Holtshad20/OMC_WIFI/AutoConnect/docs/images/rest_client.png

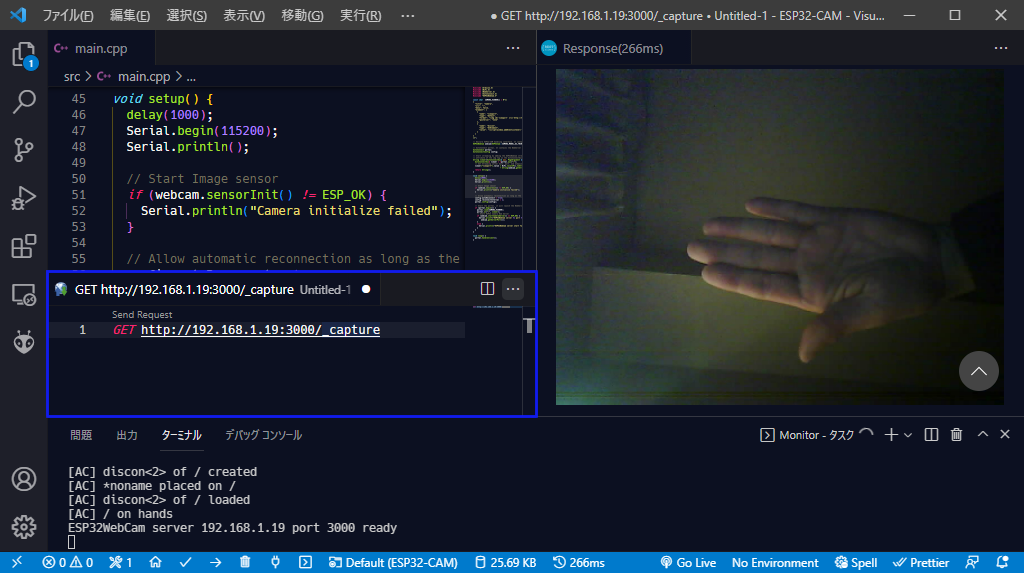
AutoConnect/docs/images/rest_client.png
