Holtshad20/OMC_WIFI/AutoConnect/docs/images/vscode_clean.png

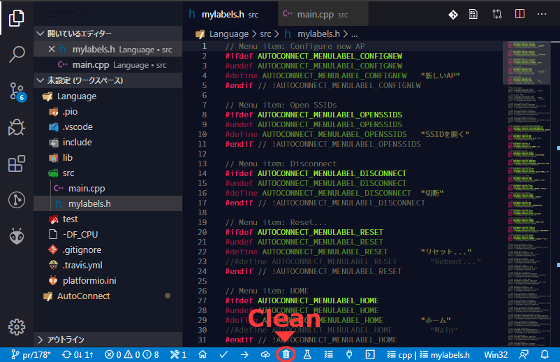
AutoConnect/docs/images/vscode_clean.png
