Holtshad20/OMC_WIFI/1.1 PZEM.jpeg

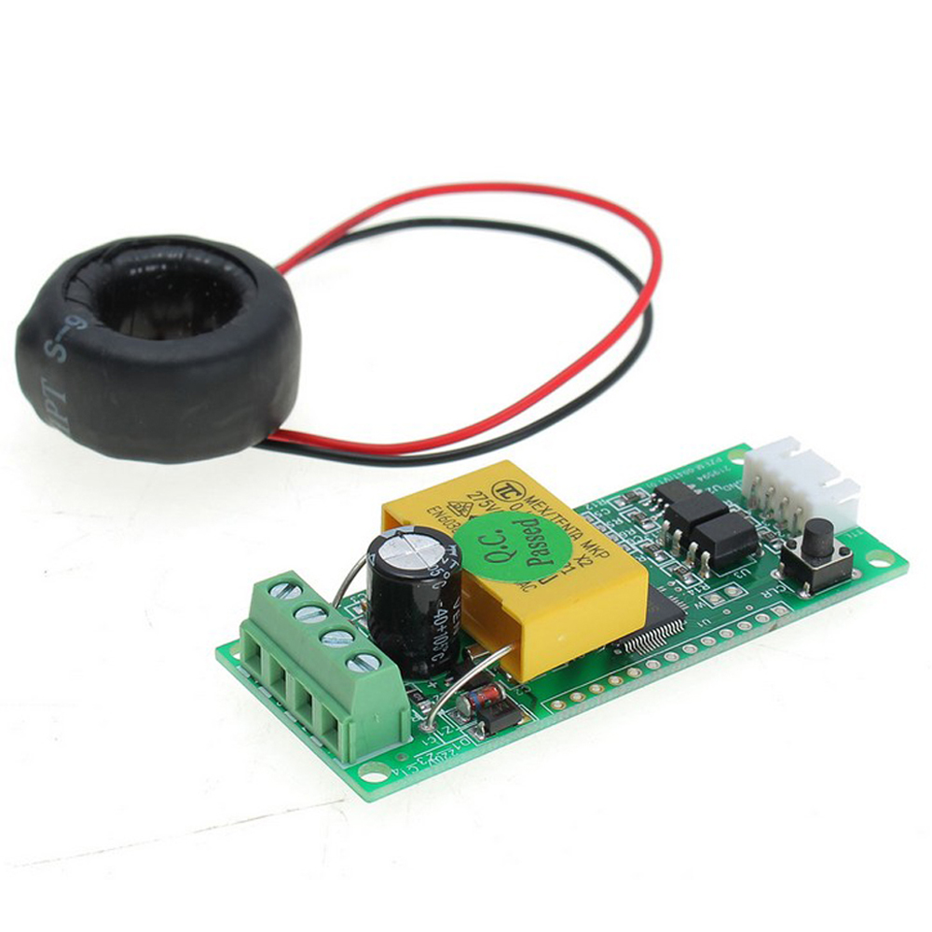
1.1 PZEM.jpeg
