Holtshad20/OMC_WIFI/1.2 SLA.jpg

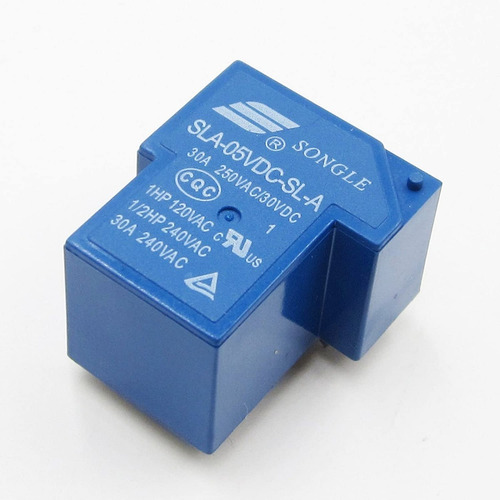
1.2 SLA.jpg
