Holtshad20/OMC_WIFI/1.3 HLK-PM01.jpg

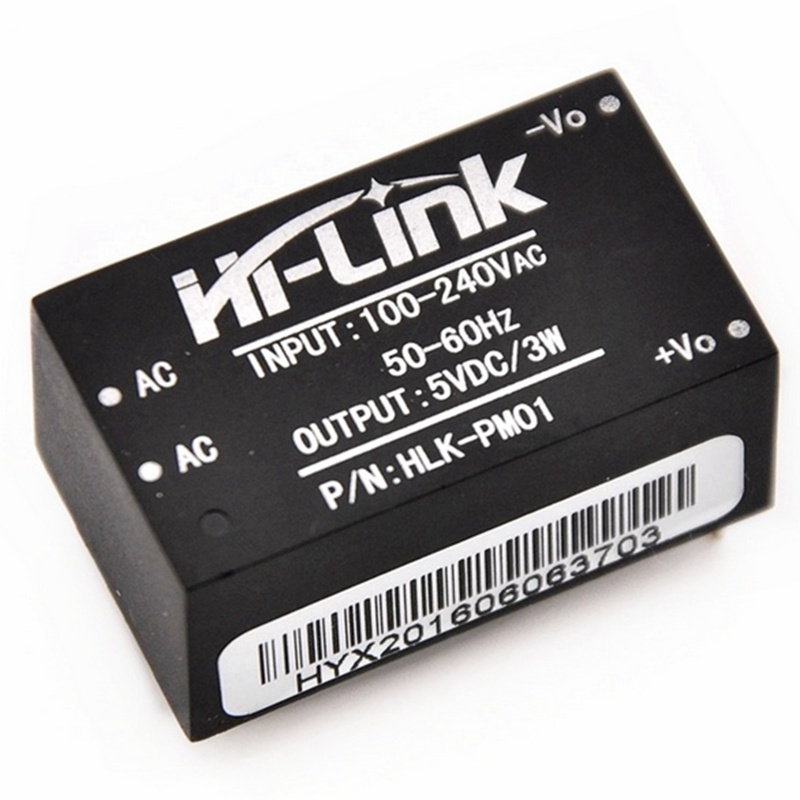
1.3 HLK-PM01.jpg
