Holtshad20/OMC_WIFI/AutoConnect/docs/images/ac2.gif

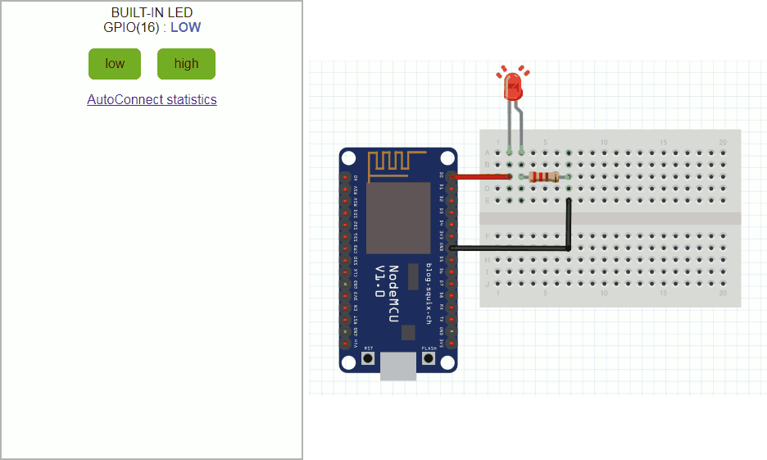
AutoConnect/docs/images/ac2.gif
