Holtshad20/OMC_WIFI/AutoConnect/docs/images/ac.png

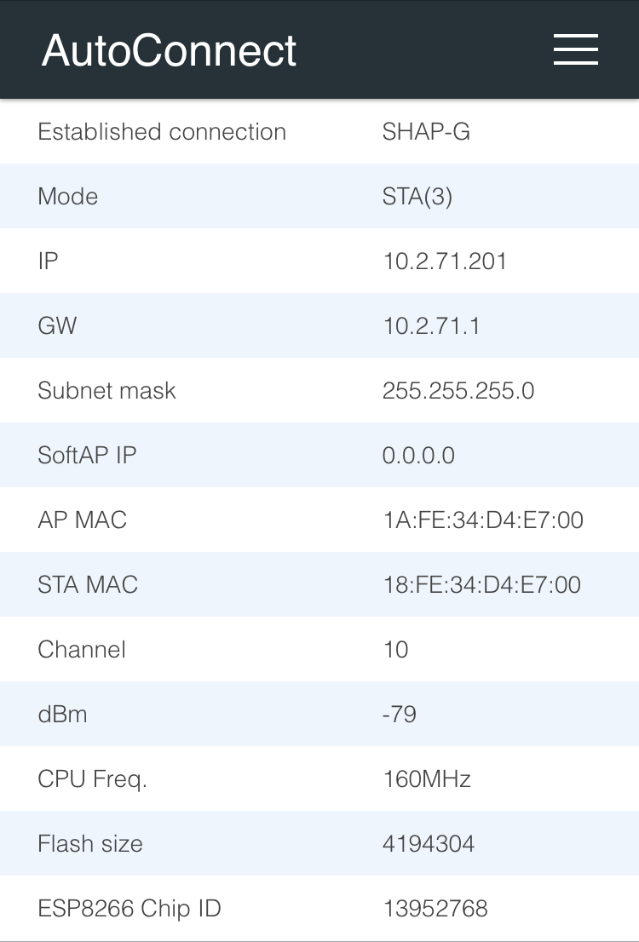
AutoConnect/docs/images/ac.png
