Holtshad20/OMC_WIFI/AutoConnect/docs/images/ac_auxmenu.png

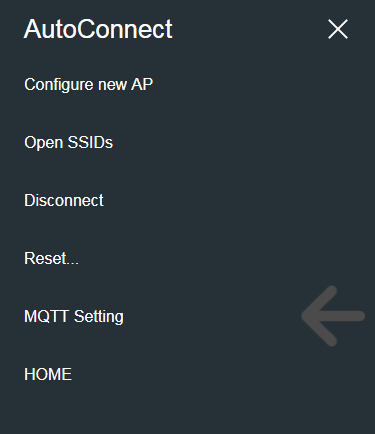
AutoConnect/docs/images/ac_auxmenu.png
