Holtshad20/OMC_WIFI/AutoConnect/docs/images/ac_auxmenu_multi.png

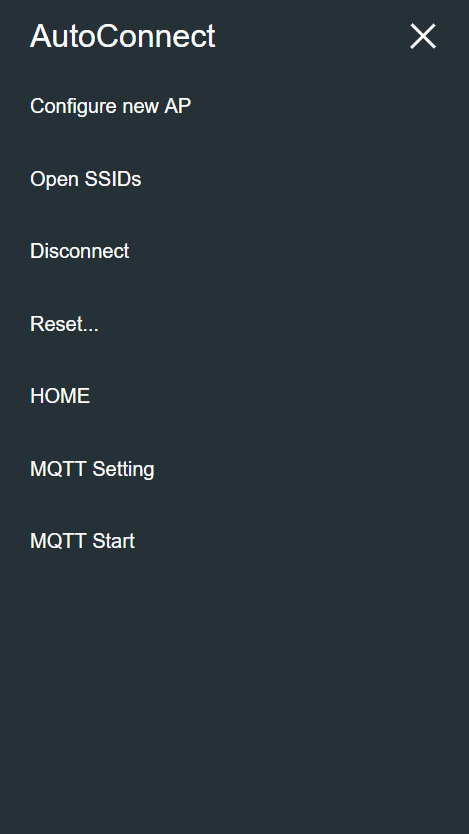
AutoConnect/docs/images/ac_auxmenu_multi.png
