Holtshad20/OMC_WIFI/AutoConnect/docs/images/ac_json.png

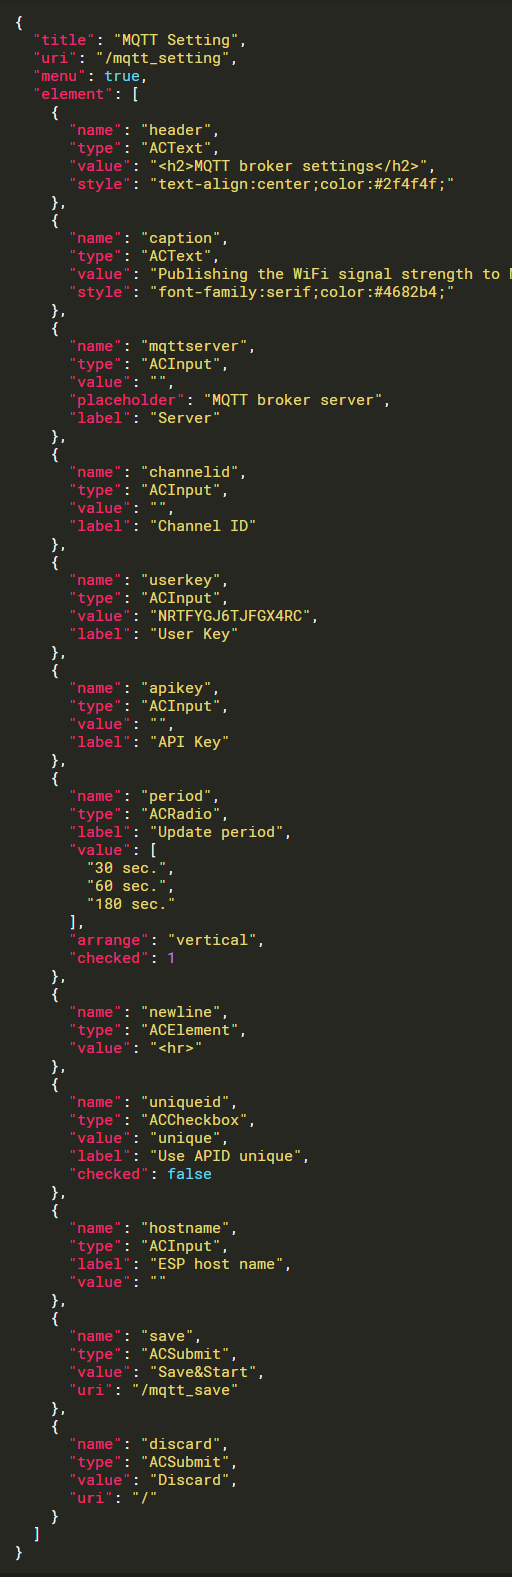
AutoConnect/docs/images/ac_json.png
