Holtshad20/OMC_WIFI/AutoConnect/docs/images/ac_mqtt_setting.png

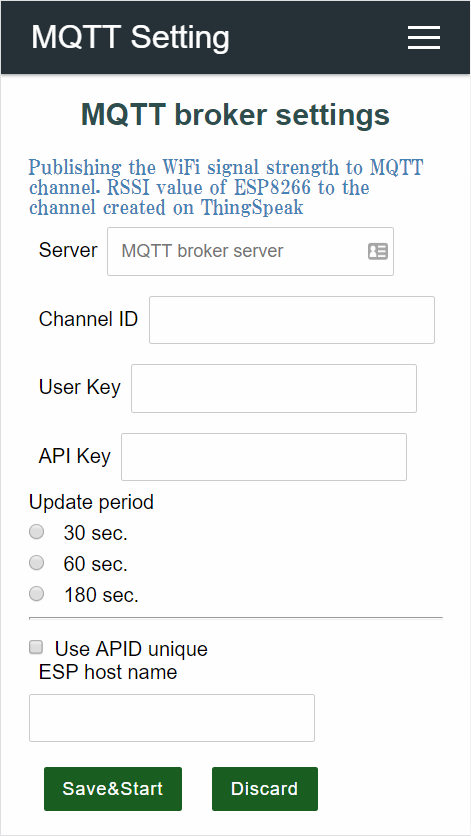
AutoConnect/docs/images/ac_mqtt_setting.png
