Holtshad20/OMC_WIFI/AutoConnect/docs/images/ACMenu_indigo.png

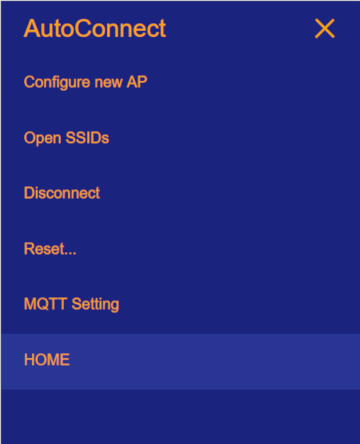
AutoConnect/docs/images/ACMenu_indigo.png
