Holtshad20/OMC_WIFI/AutoConnect/docs/images/acow.png

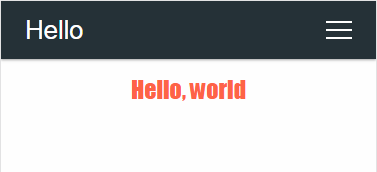
AutoConnect/docs/images/acow.png
