Holtshad20/OMC_WIFI/AutoConnect/docs/images/acselect.png

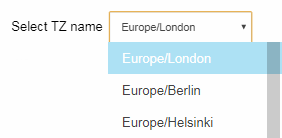
AutoConnect/docs/images/acselect.png
