Holtshad20/OMC_WIFI/AutoConnect/docs/images/adder.png

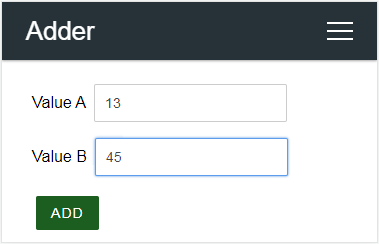
AutoConnect/docs/images/adder.png
