Holtshad20/OMC_WIFI/AutoConnect/docs/images/addmenu.gif

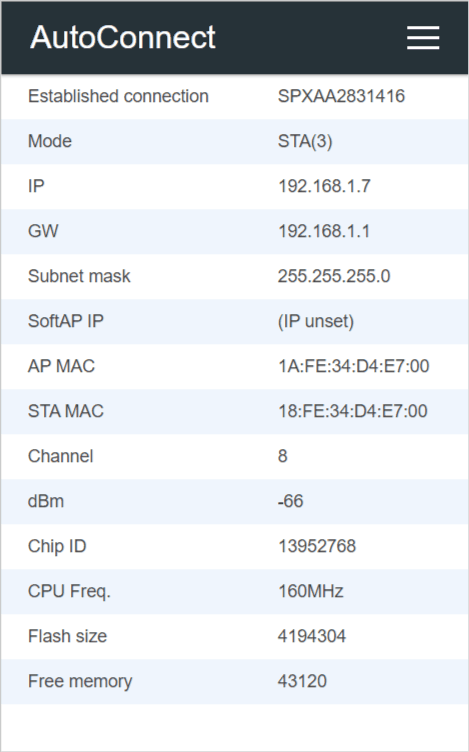
AutoConnect/docs/images/addmenu.gif
