Holtshad20/OMC_WIFI/AutoConnect/docs/images/answer.png

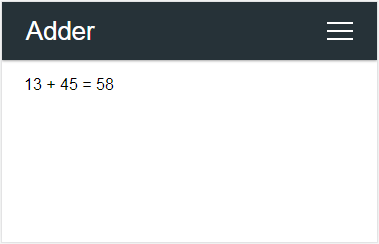
AutoConnect/docs/images/answer.png
