Holtshad20/OMC_WIFI/AutoConnect/docs/images/APIKeys.png

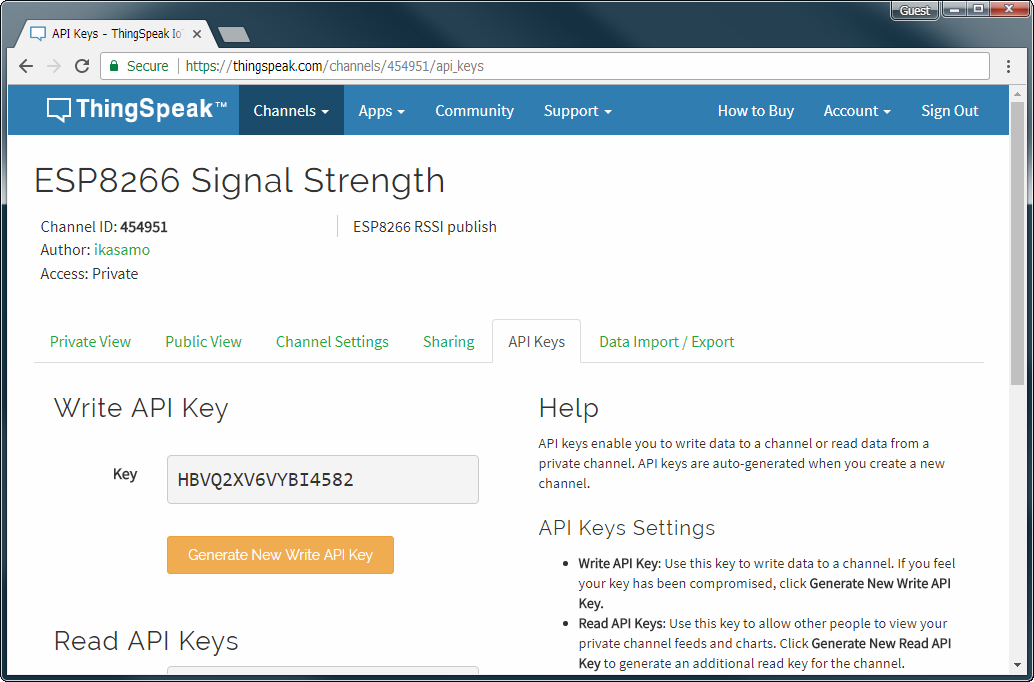
AutoConnect/docs/images/APIKeys.png
