Holtshad20/OMC_WIFI/AutoConnect/docs/images/applymenu.png

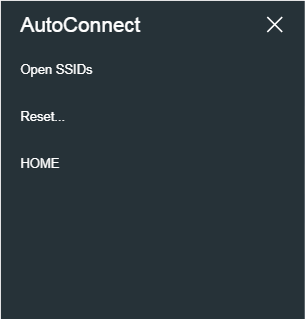
AutoConnect/docs/images/applymenu.png
