Holtshad20/OMC_WIFI/AutoConnect/docs/images/AutoConnectAux.gif

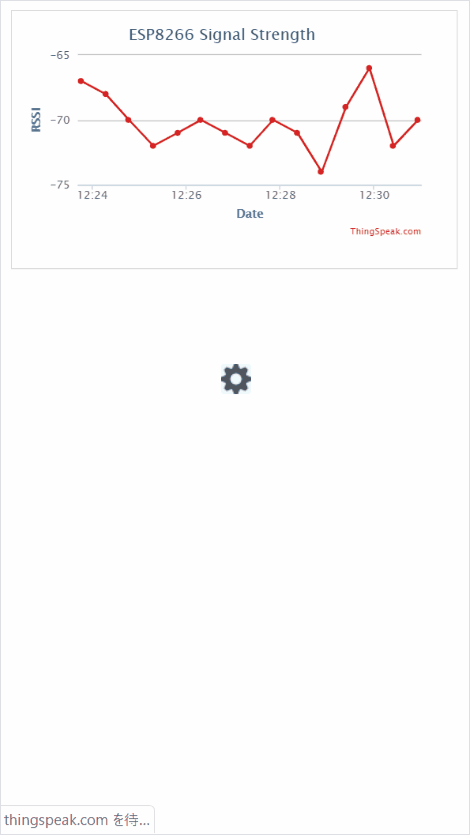
AutoConnect/docs/images/AutoConnectAux.gif
