Holtshad20/OMC_WIFI/AutoConnect/docs/images/aux_fsbrowser.gif

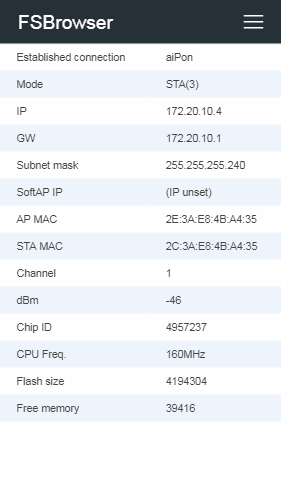
AutoConnect/docs/images/aux_fsbrowser.gif
