Holtshad20/OMC_WIFI/AutoConnect/docs/images/aux_json.png

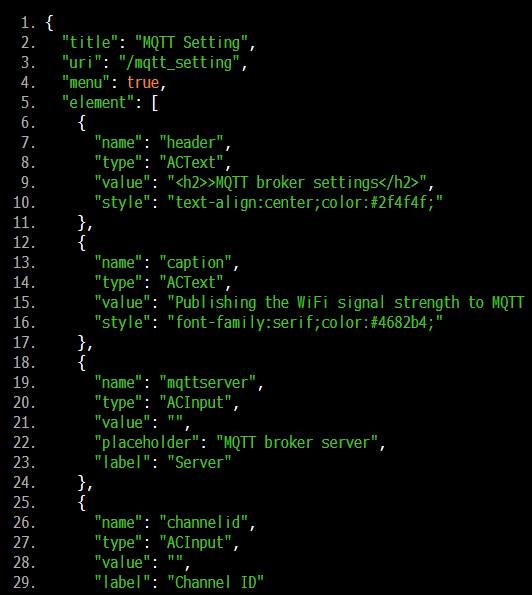
AutoConnect/docs/images/aux_json.png
