Holtshad20/OMC_WIFI/AutoConnect/docs/images/aux_ov.gif

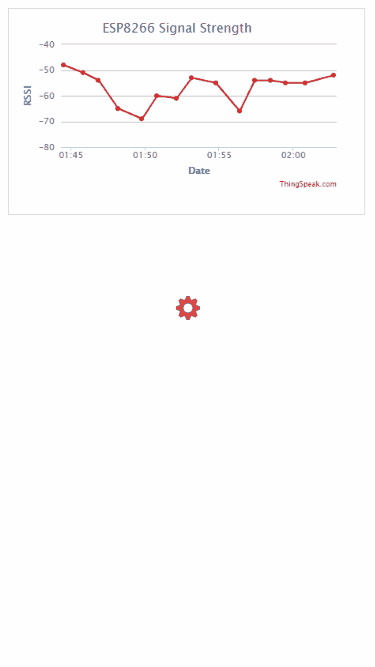
AutoConnect/docs/images/aux_ov.gif
