Holtshad20/OMC_WIFI/AutoConnect/docs/images/aux_pattern.gif

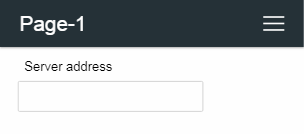
AutoConnect/docs/images/aux_pattern.gif
