Holtshad20/OMC_WIFI/AutoConnect/docs/images/beforeafter.png

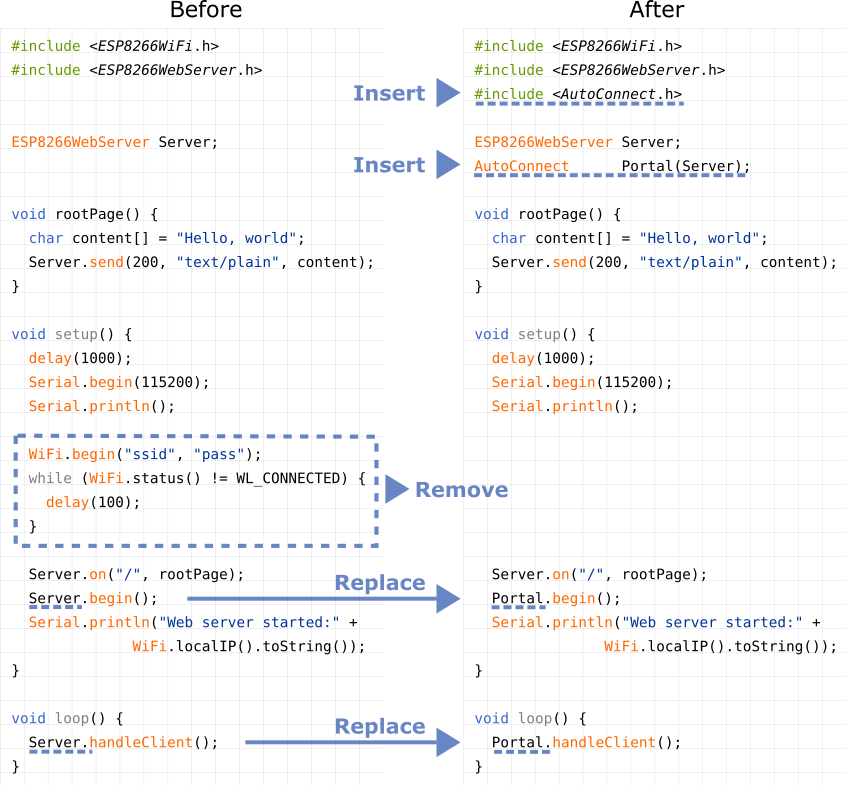
AutoConnect/docs/images/beforeafter.png
