Holtshad20/OMC_WIFI/AutoConnect/docs/images/begin.png

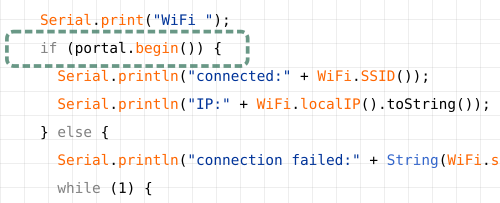
AutoConnect/docs/images/begin.png
