Holtshad20/OMC_WIFI/AutoConnect/docs/images/ChannelID.png

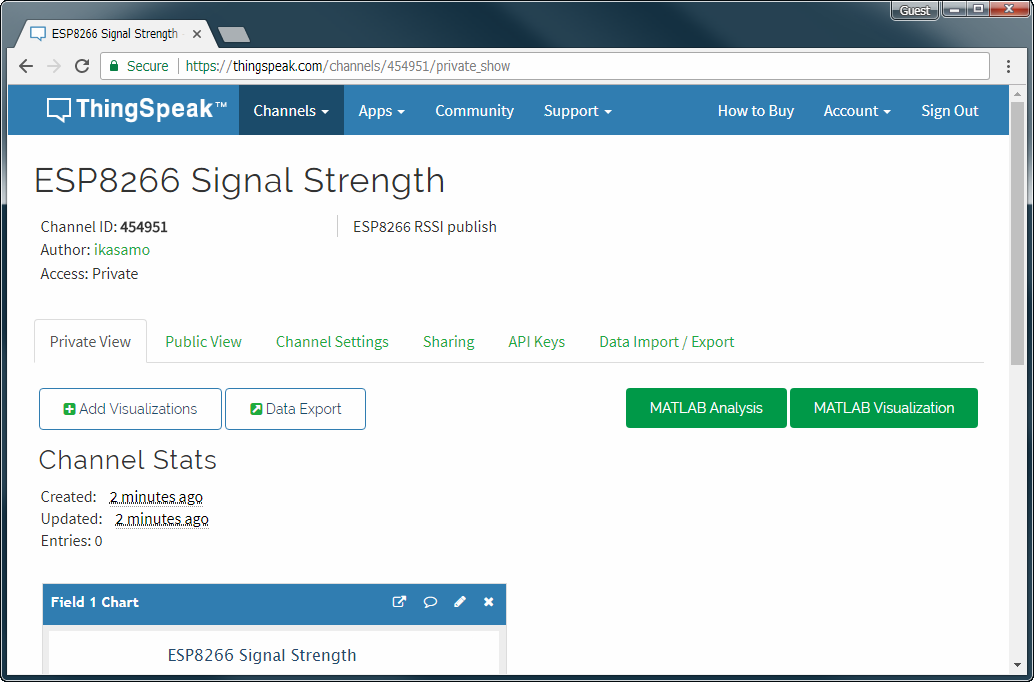
AutoConnect/docs/images/ChannelID.png
