Holtshad20/OMC_WIFI/AutoConnect/docs/images/ChannelStatus.png

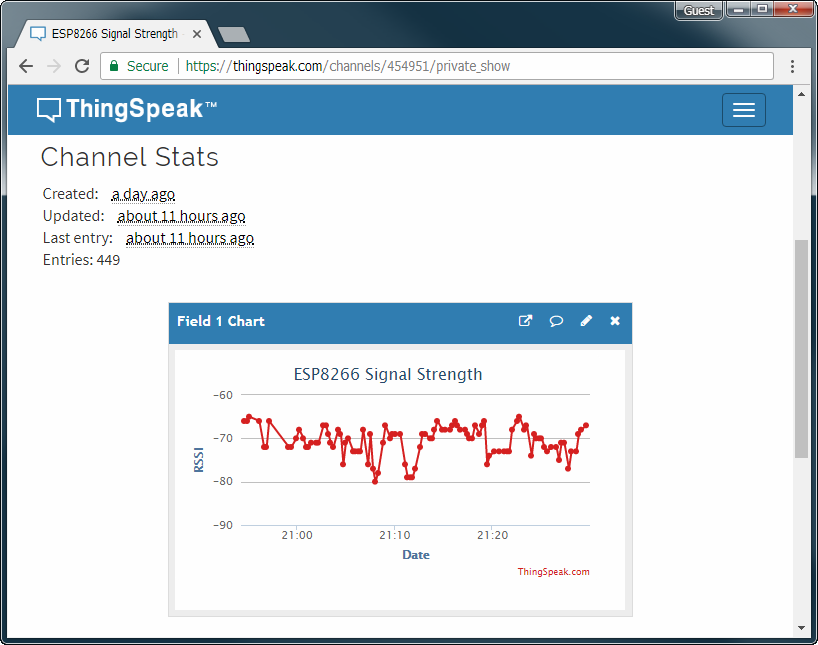
AutoConnect/docs/images/ChannelStatus.png
