Holtshad20/OMC_WIFI/AutoConnect/docs/images/config_ssid.png

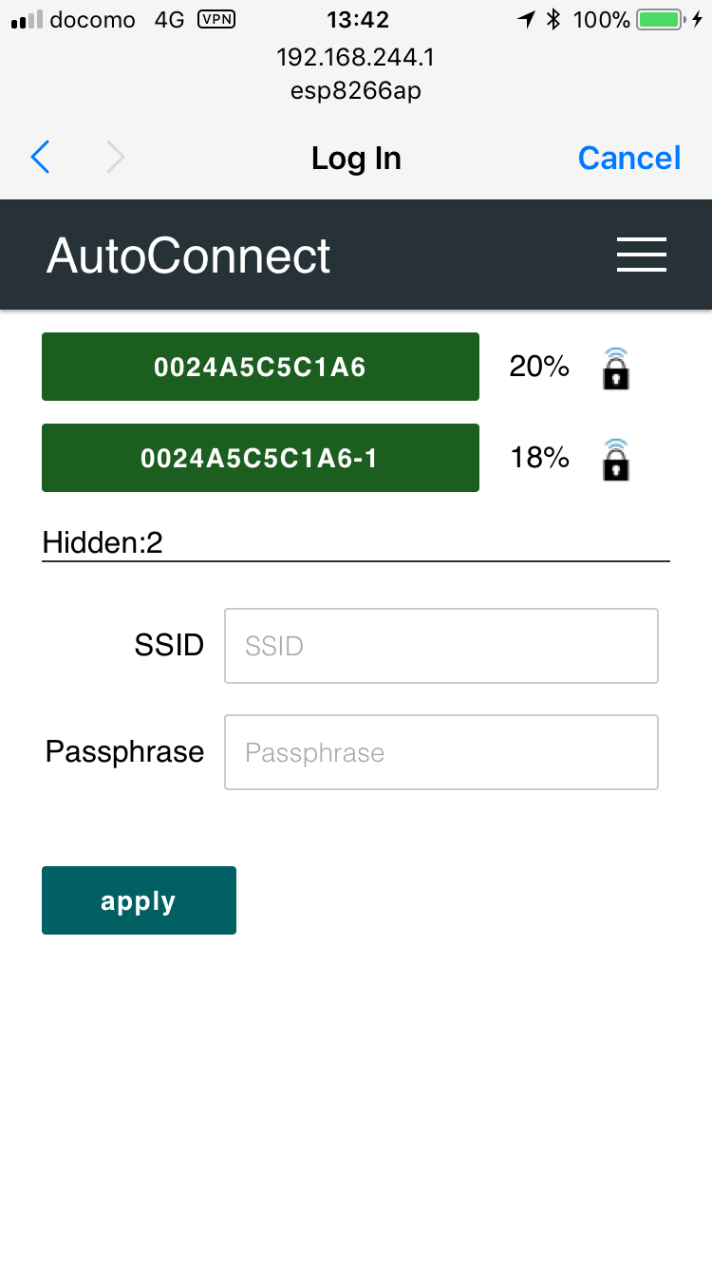
AutoConnect/docs/images/config_ssid.png
