Holtshad20/OMC_WIFI/AutoConnect/docs/images/confignew.png

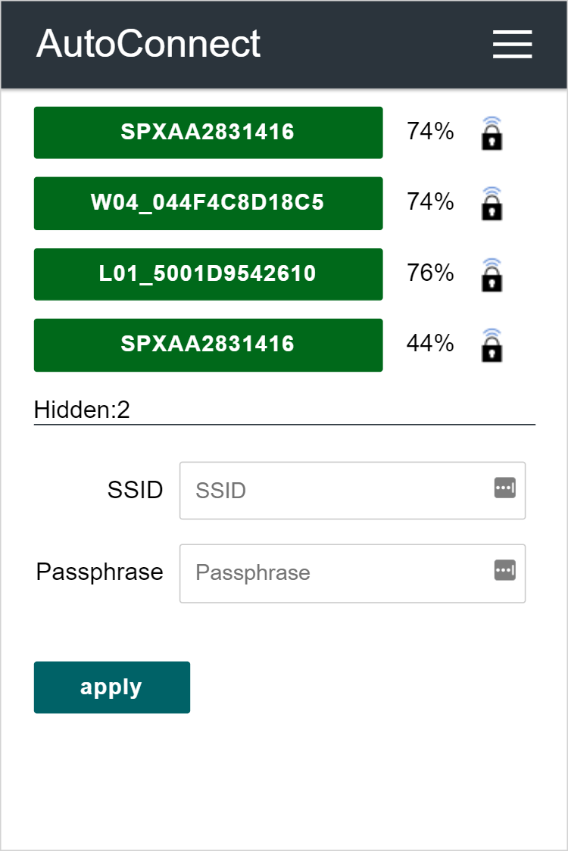
AutoConnect/docs/images/confignew.png
