Holtshad20/OMC_WIFI/AutoConnect/docs/images/CreateChannel.png

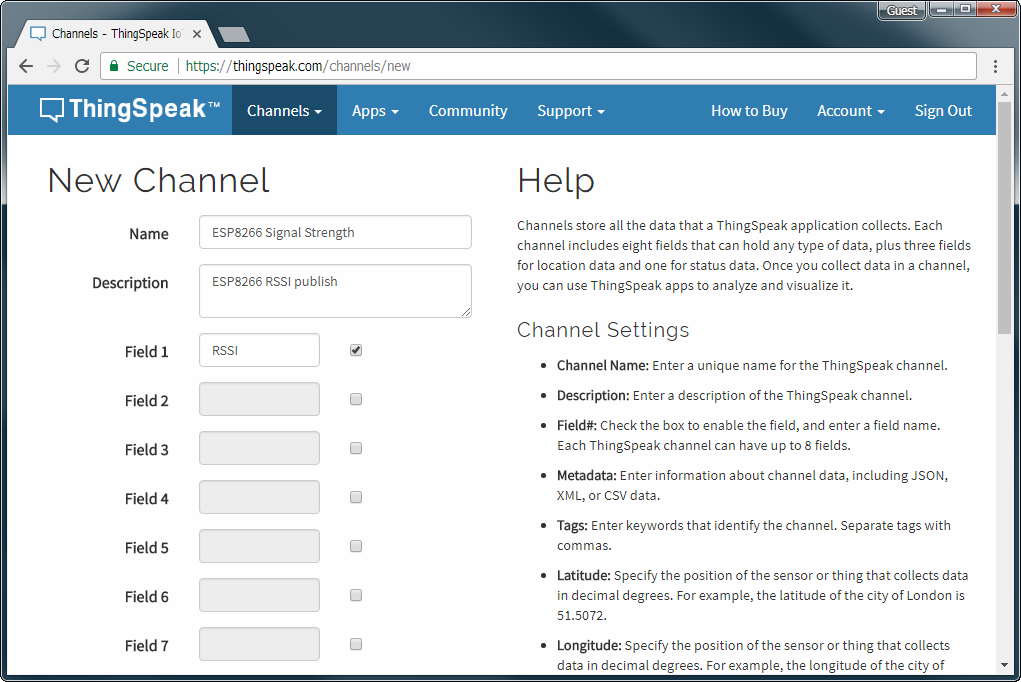
AutoConnect/docs/images/CreateChannel.png
