Holtshad20/OMC_WIFI/AutoConnect/docs/images/creditmigrate.png

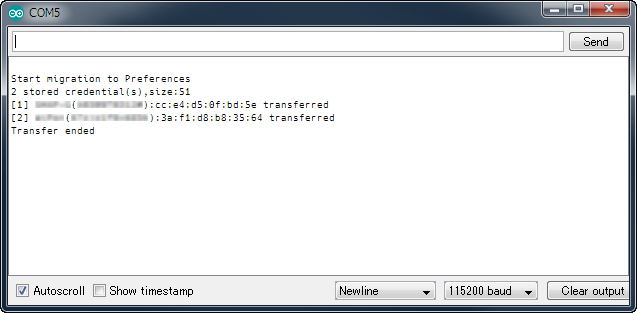
AutoConnect/docs/images/creditmigrate.png
