Holtshad20/OMC_WIFI/AutoConnect/docs/images/esp32cam_view.png

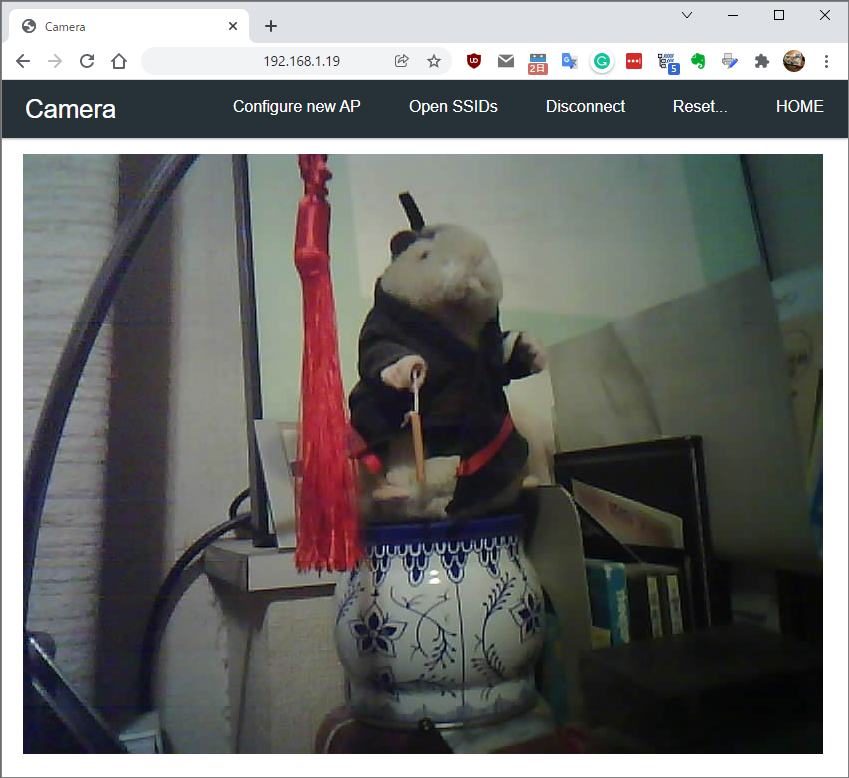
AutoConnect/docs/images/esp32cam_view.png
