Holtshad20/OMC_WIFI/AutoConnect/docs/images/espshaker.gif

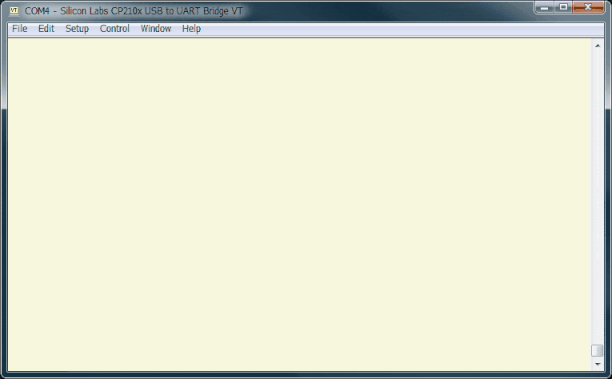
AutoConnect/docs/images/espshaker.gif
