Holtshad20/OMC_WIFI/AutoConnect/docs/images/established.png

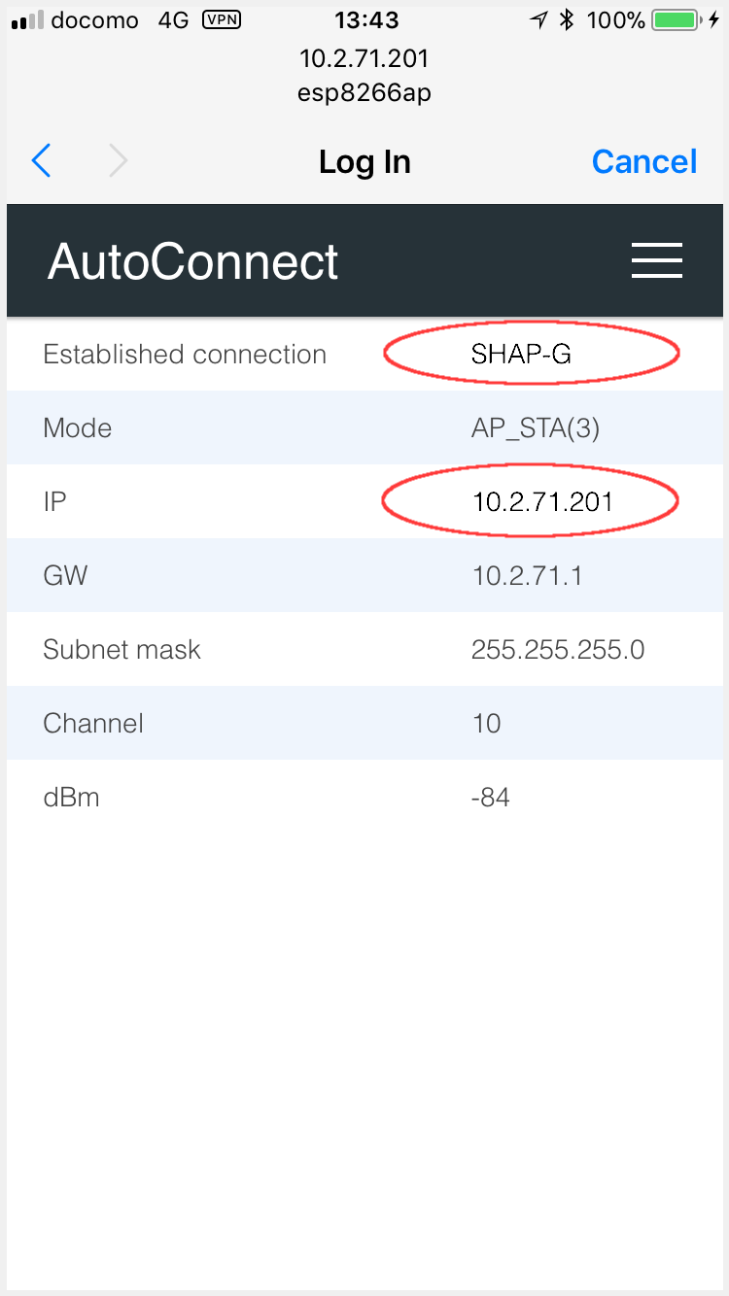
AutoConnect/docs/images/established.png
