Holtshad20/OMC_WIFI/AutoConnect/docs/images/export_binary.png

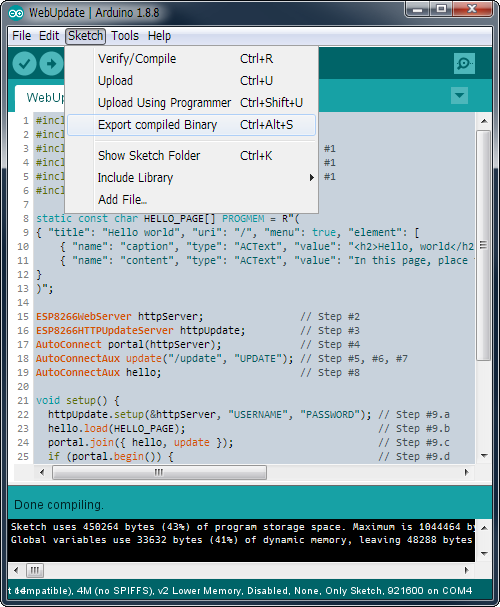
AutoConnect/docs/images/export_binary.png
