Holtshad20/OMC_WIFI/AutoConnect/docs/images/extswitch.png

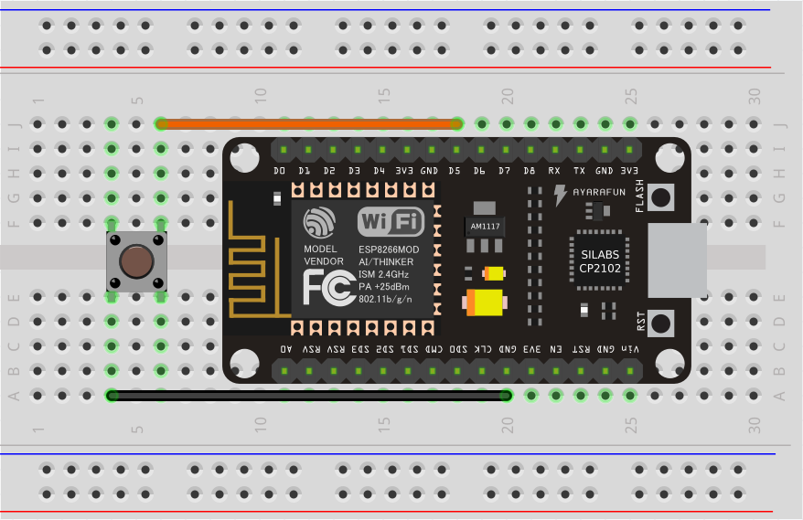
AutoConnect/docs/images/extswitch.png
