Holtshad20/OMC_WIFI/AutoConnect/docs/images/gitrepo.png

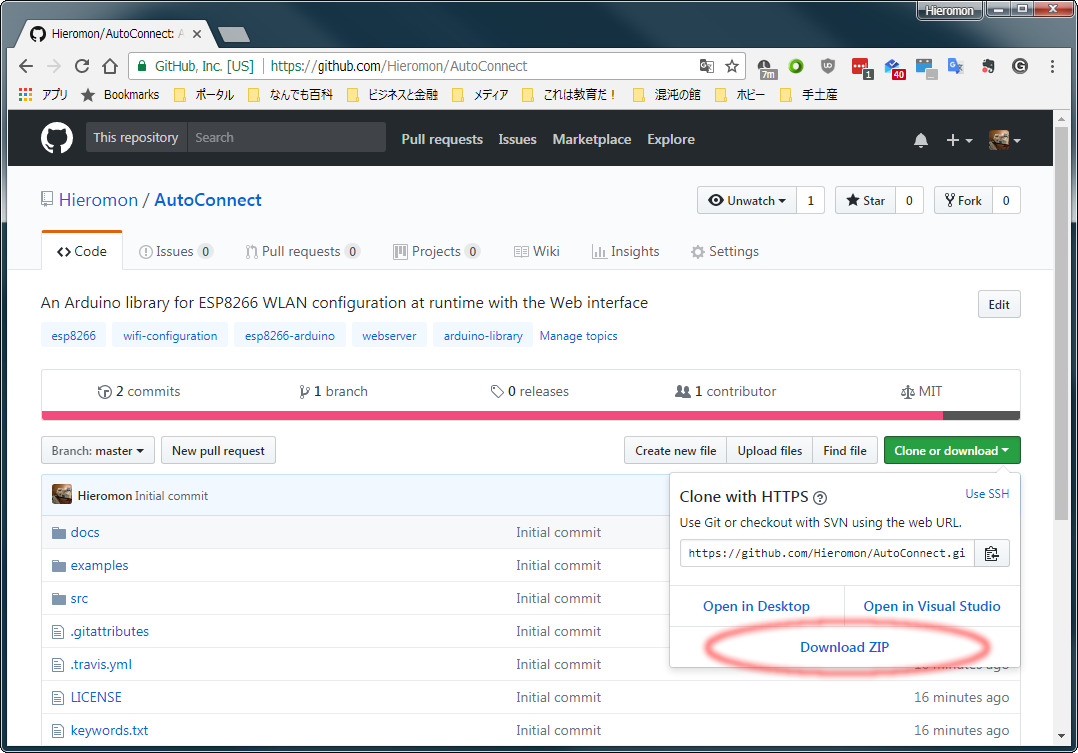
AutoConnect/docs/images/gitrepo.png
