Holtshad20/OMC_WIFI/AutoConnect/docs/images/global1.png

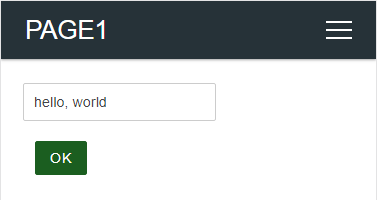
AutoConnect/docs/images/global1.png
