Holtshad20/OMC_WIFI/AutoConnect/docs/images/global2.png

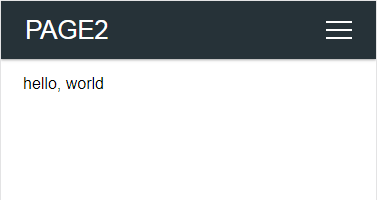
AutoConnect/docs/images/global2.png
