Holtshad20/OMC_WIFI/AutoConnect/docs/images/handleClient.png

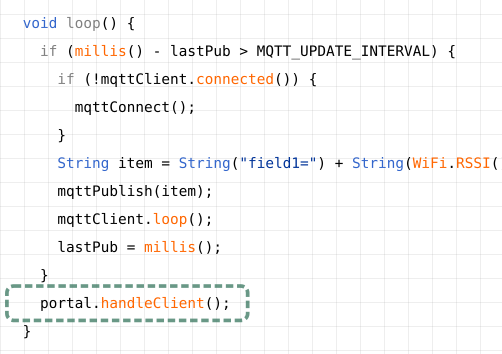
AutoConnect/docs/images/handleClient.png
