Holtshad20/OMC_WIFI/AutoConnect/docs/images/heartbeat.png

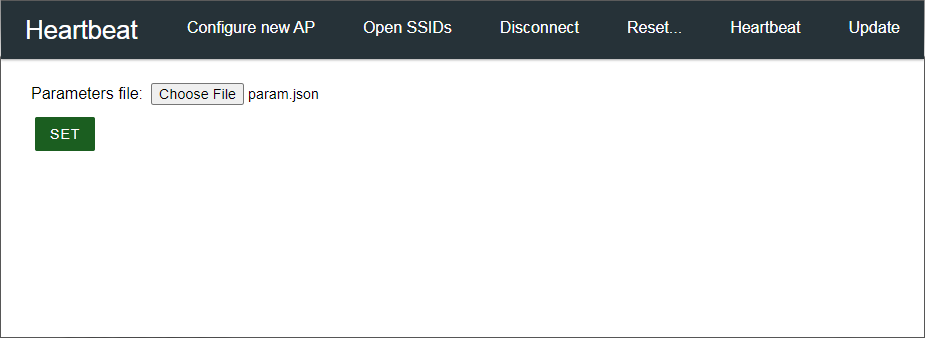
AutoConnect/docs/images/heartbeat.png
