Holtshad20/OMC_WIFI/AutoConnect/docs/images/hello_world.png

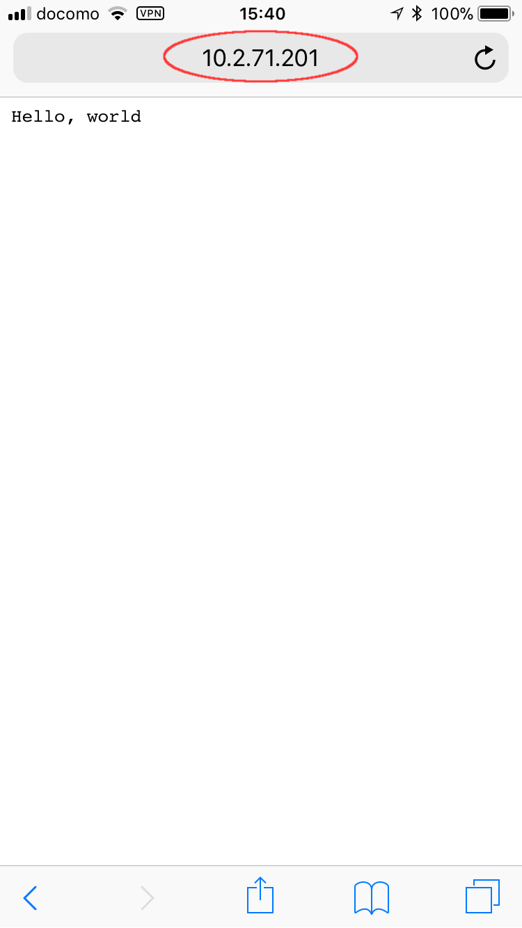
AutoConnect/docs/images/hello_world.png
