Holtshad20/OMC_WIFI/AutoConnect/docs/images/html5_forms_number.png

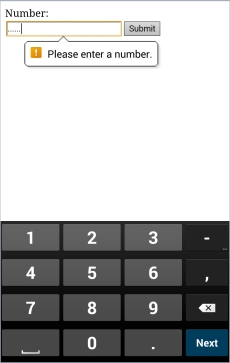
AutoConnect/docs/images/html5_forms_number.png
