Holtshad20/OMC_WIFI/AutoConnect/docs/images/html5_forms_number_ios.png

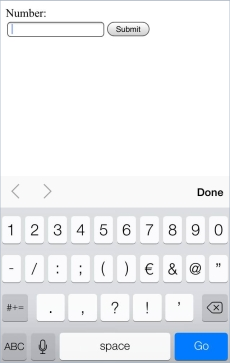
AutoConnect/docs/images/html5_forms_number_ios.png
