Holtshad20/OMC_WIFI/AutoConnect/docs/images/include.png

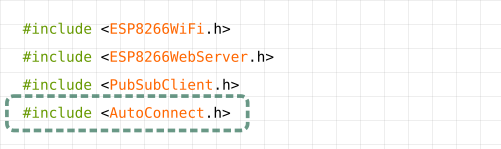
AutoConnect/docs/images/include.png
