Holtshad20/OMC_WIFI/AutoConnect/docs/images/ins_lib.png

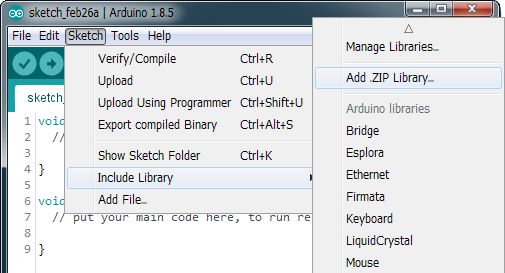
AutoConnect/docs/images/ins_lib.png
