Holtshad20/OMC_WIFI/AutoConnect/docs/images/lm.png

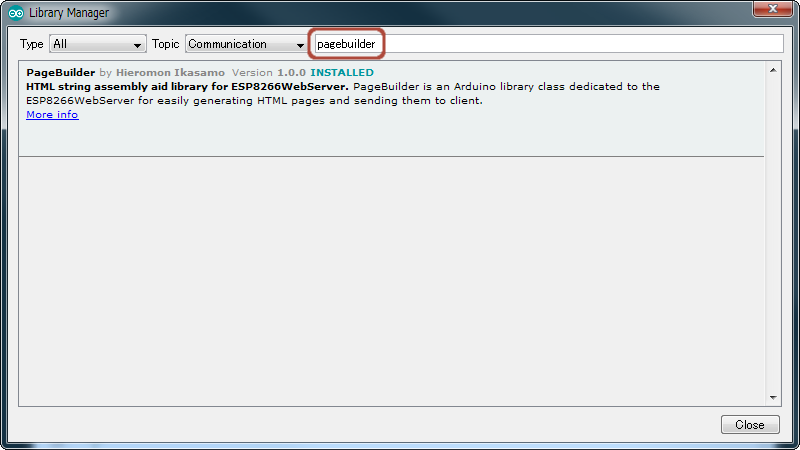
AutoConnect/docs/images/lm.png
