Holtshad20/OMC_WIFI/AutoConnect/docs/images/localize.png

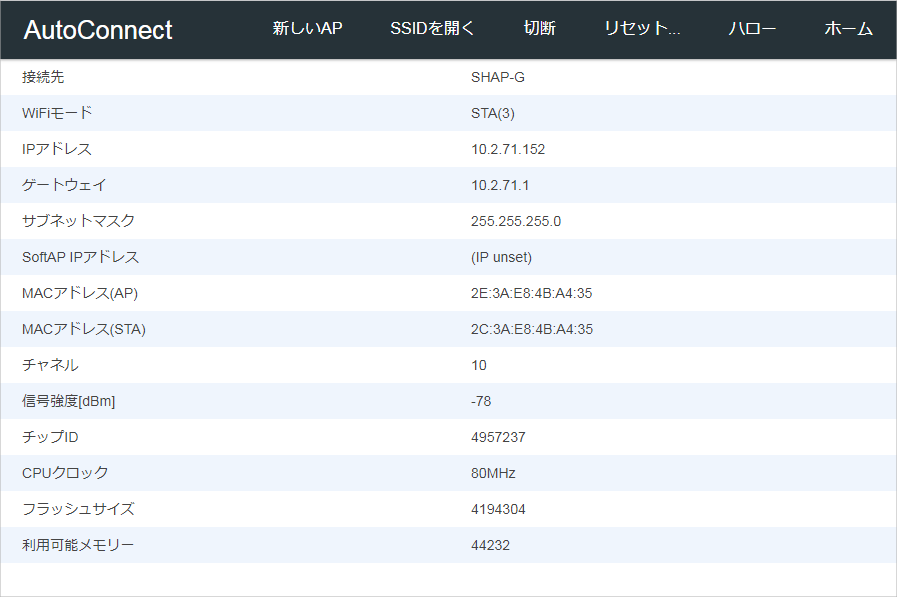
AutoConnect/docs/images/localize.png
