Holtshad20/OMC_WIFI/AutoConnect/docs/images/login.png

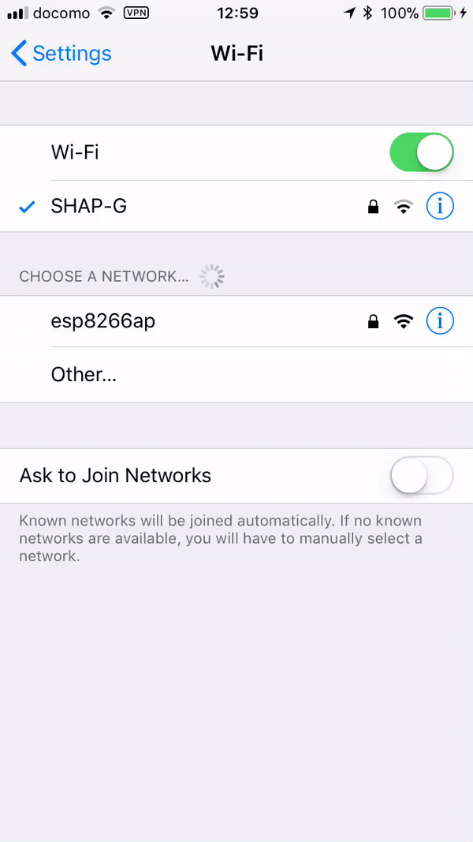
AutoConnect/docs/images/login.png
