Holtshad20/OMC_WIFI/AutoConnect/docs/images/menu_home.png

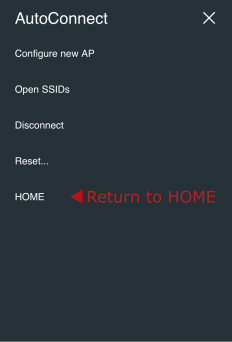
AutoConnect/docs/images/menu_home.png
