Holtshad20/OMC_WIFI/AutoConnect/docs/images/menu_login.png

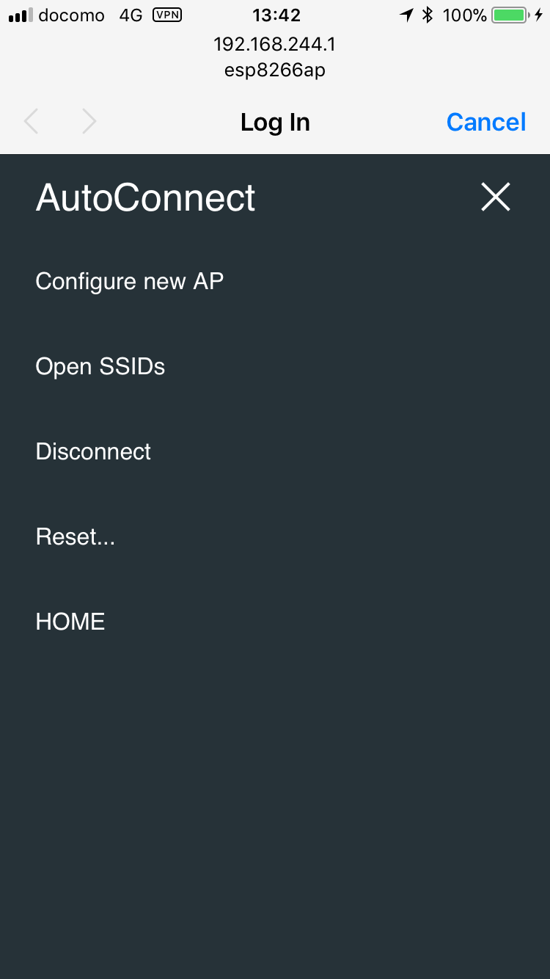
AutoConnect/docs/images/menu_login.png
