Holtshad20/OMC_WIFI/AutoConnect/docs/images/newap.png

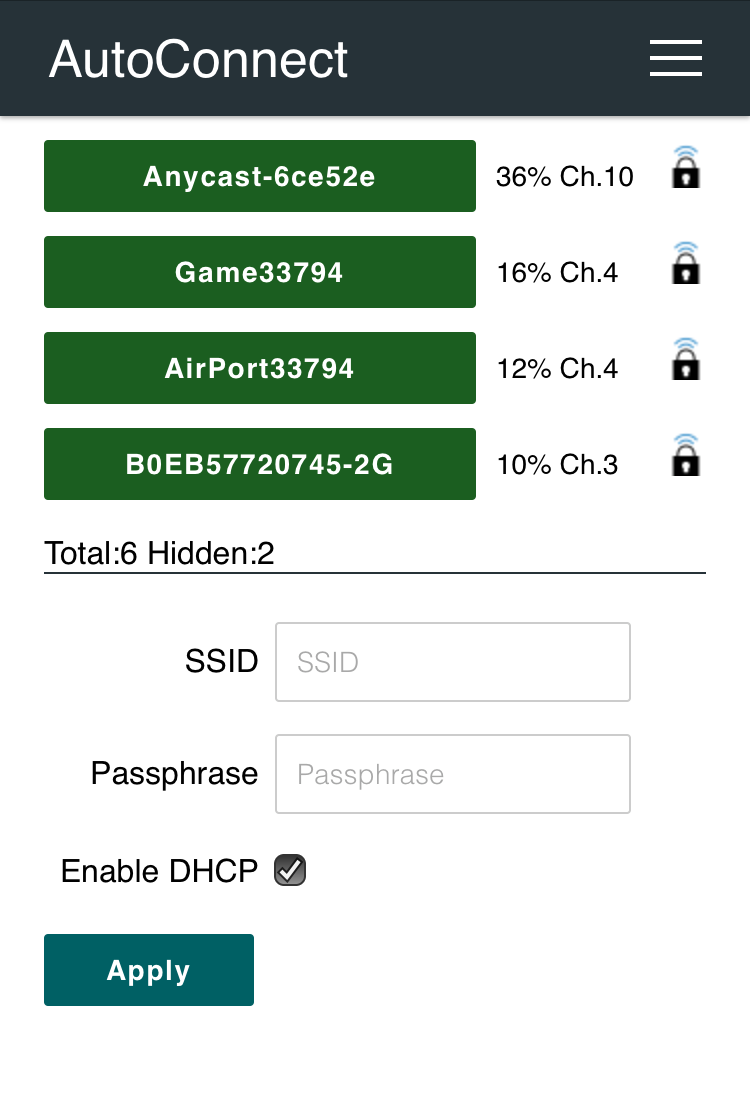
AutoConnect/docs/images/newap.png
