Holtshad20/OMC_WIFI/AutoConnect/docs/images/newap_static.png

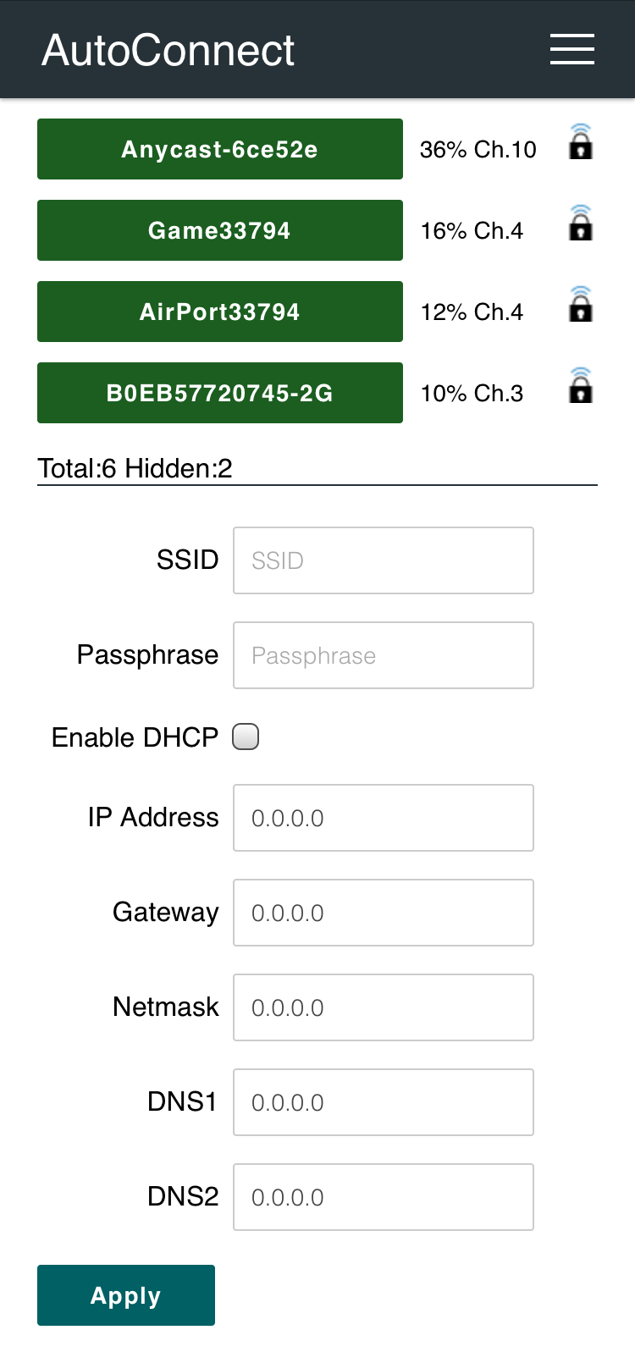
AutoConnect/docs/images/newap_static.png
