Holtshad20/OMC_WIFI/AutoConnect/docs/images/openssid.png

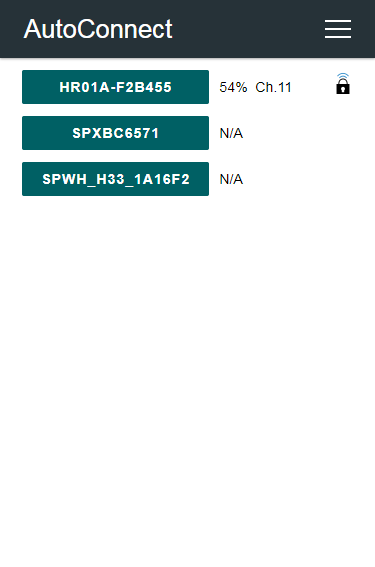
AutoConnect/docs/images/openssid.png
