Holtshad20/OMC_WIFI/AutoConnect/docs/images/openssid_trash.png

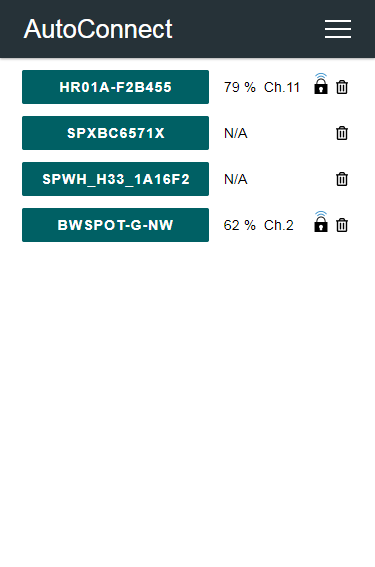
AutoConnect/docs/images/openssid_trash.png
