Holtshad20/OMC_WIFI/AutoConnect/docs/images/otacaption.png

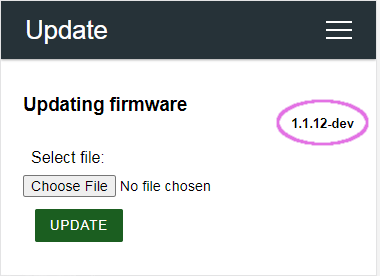
AutoConnect/docs/images/otacaption.png
