Holtshad20/OMC_WIFI/AutoConnect/docs/images/ov.gif

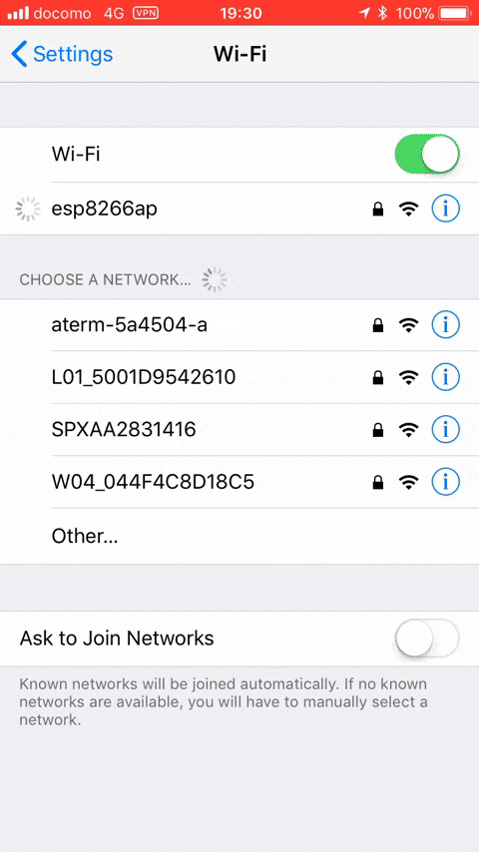
AutoConnect/docs/images/ov.gif
