Holtshad20/OMC_WIFI/AutoConnect/docs/images/ov.png

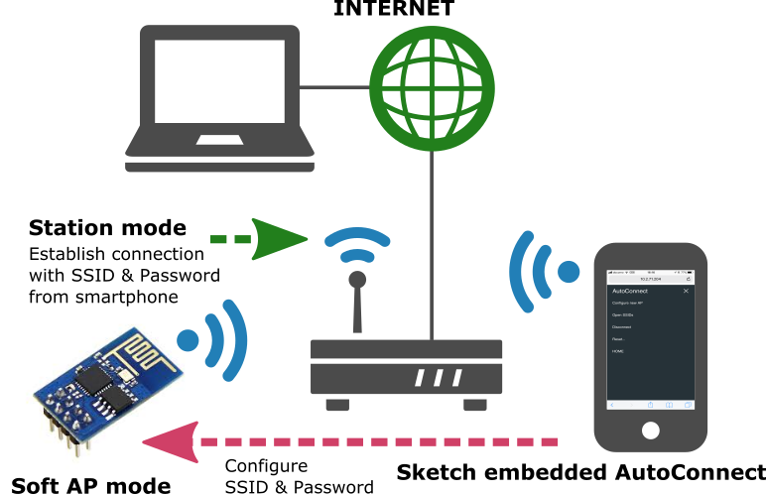
AutoConnect/docs/images/ov.png
