Holtshad20/OMC_WIFI/AutoConnect/docs/images/partition.png

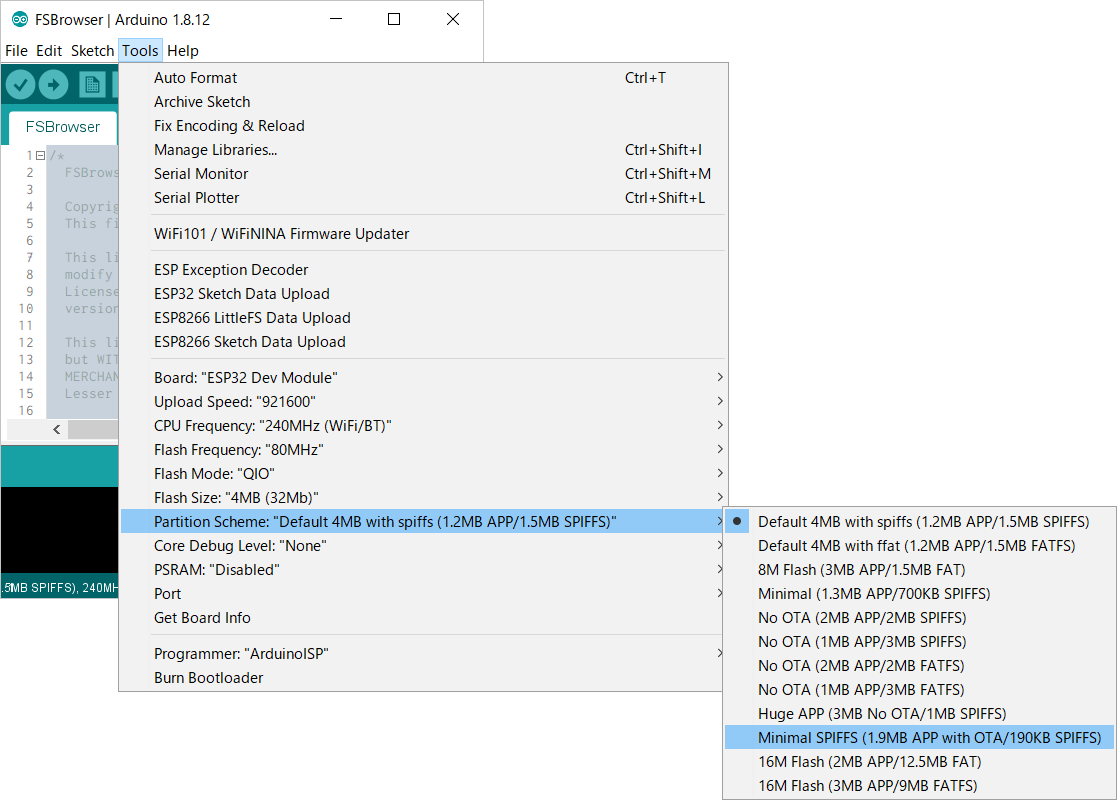
AutoConnect/docs/images/partition.png
