Holtshad20/OMC_WIFI/AutoConnect/docs/images/reset.png

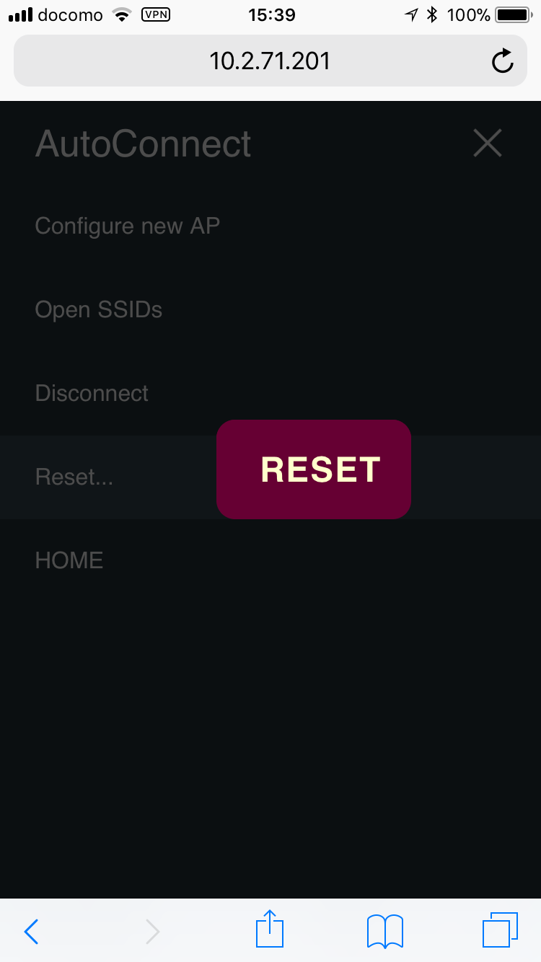
AutoConnect/docs/images/reset.png
