Holtshad20/OMC_WIFI/AutoConnect/docs/images/reset_r.png

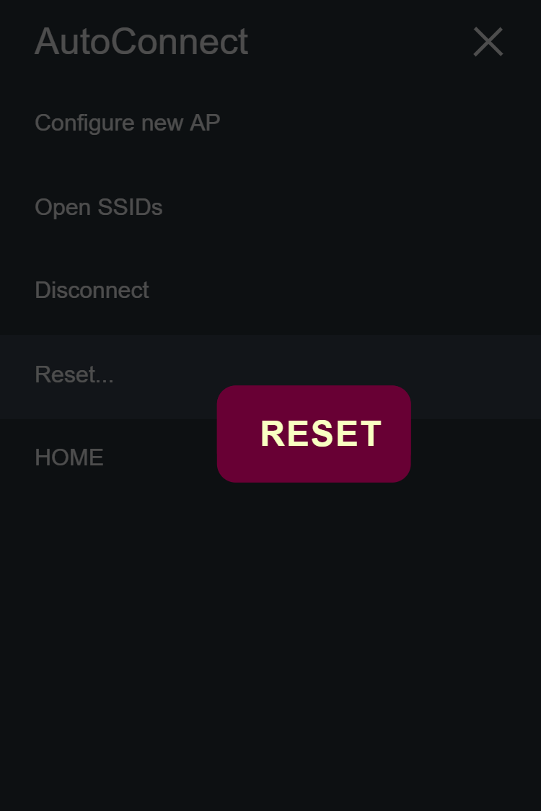
AutoConnect/docs/images/reset_r.png
