Holtshad20/OMC_WIFI/AutoConnect/docs/images/resetting.png

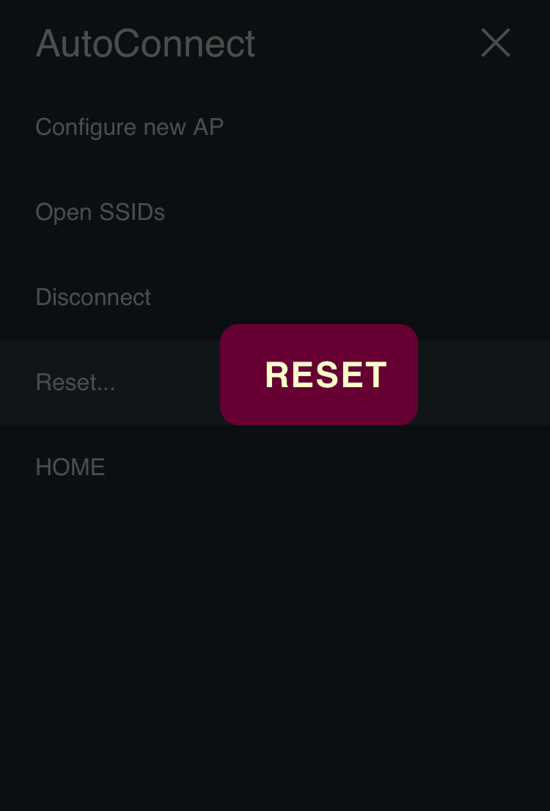
AutoConnect/docs/images/resetting.png
