Holtshad20/OMC_WIFI/AutoConnect/docs/images/rssi_chart.png

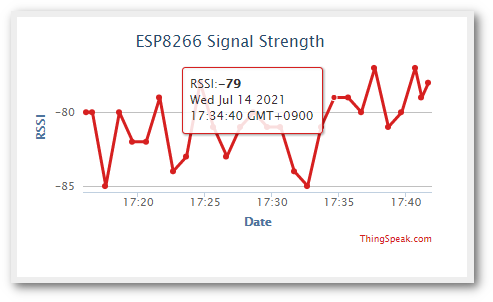
AutoConnect/docs/images/rssi_chart.png
