Holtshad20/OMC_WIFI/AutoConnect/docs/images/serial.png

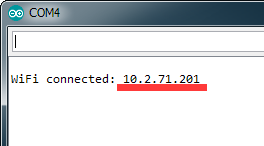
AutoConnect/docs/images/serial.png
