Holtshad20/OMC_WIFI/AutoConnect/docs/images/serverupdate.gif

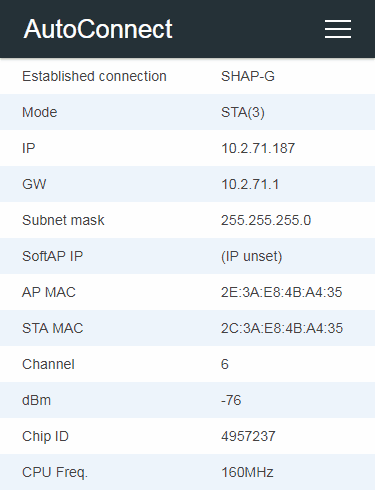
AutoConnect/docs/images/serverupdate.gif
