Holtshad20/OMC_WIFI/AutoConnect/docs/images/stat.png

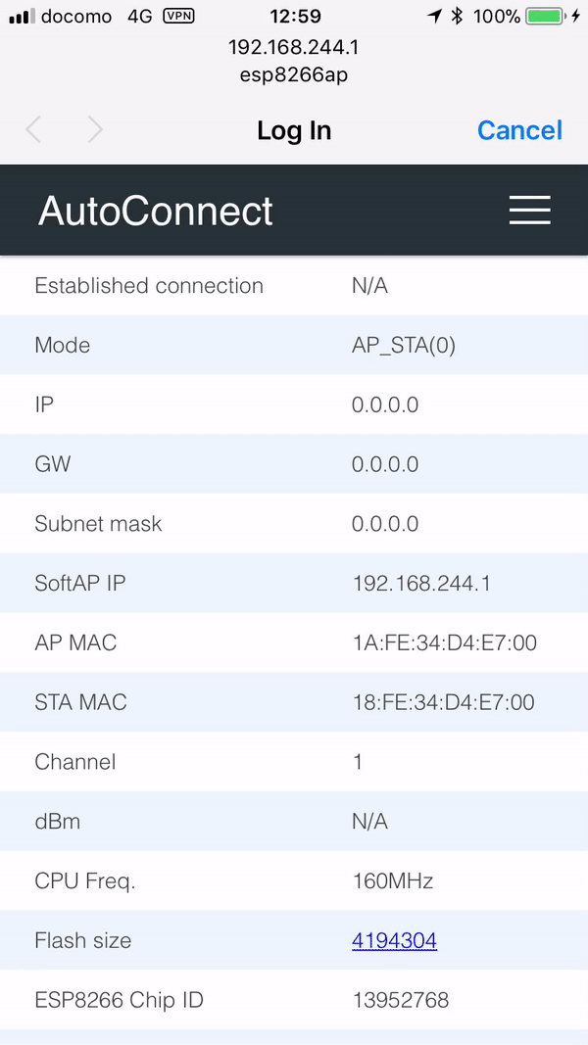
AutoConnect/docs/images/stat.png
