Holtshad20/OMC_WIFI/AutoConnect/docs/images/staticip.png

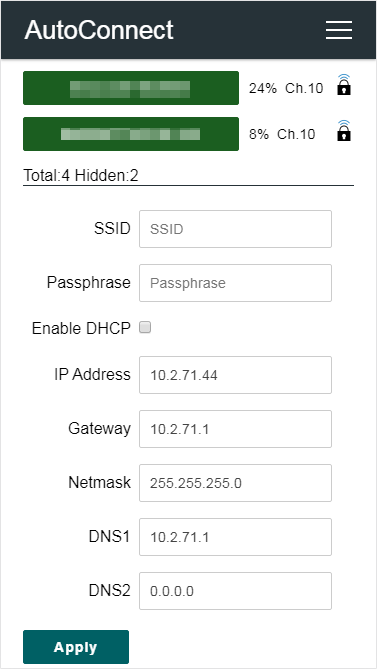
AutoConnect/docs/images/staticip.png
