Holtshad20/OMC_WIFI/AutoConnect/docs/images/statistics.png

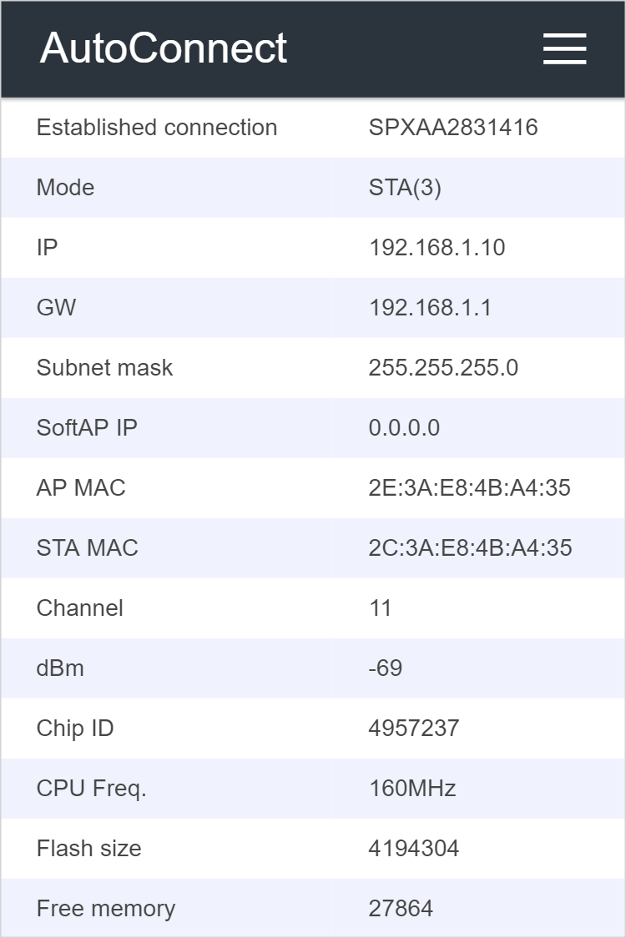
AutoConnect/docs/images/statistics.png
