Holtshad20/OMC_WIFI/AutoConnect/docs/images/updated.png

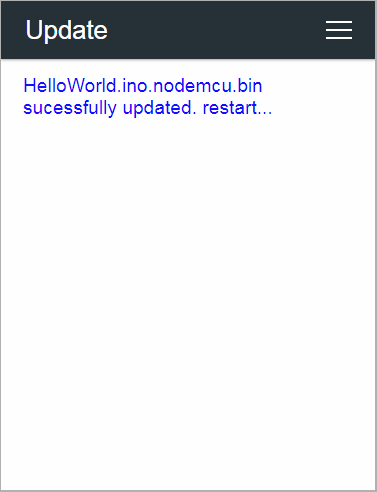
AutoConnect/docs/images/updated.png
