Holtshad20/OMC_WIFI/AutoConnect/docs/images/updatelist.png

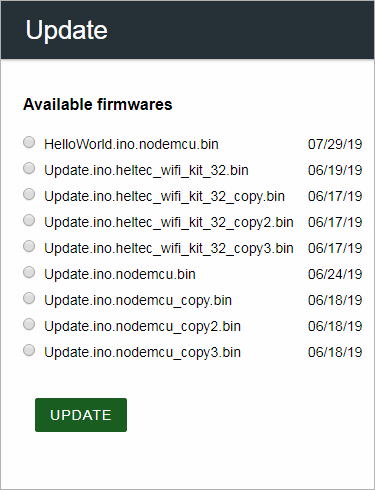
AutoConnect/docs/images/updatelist.png
