Holtshad20/OMC_WIFI/AutoConnect/docs/images/updatemenu.png

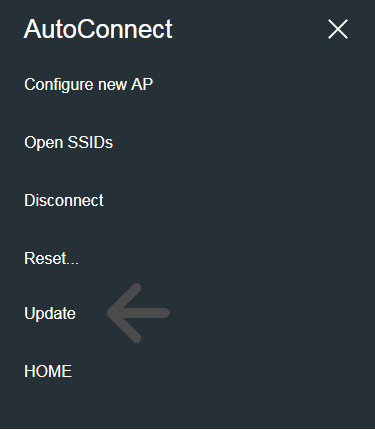
AutoConnect/docs/images/updatemenu.png
