Holtshad20/OMC_WIFI/AutoConnect/docs/images/updatemodel.png

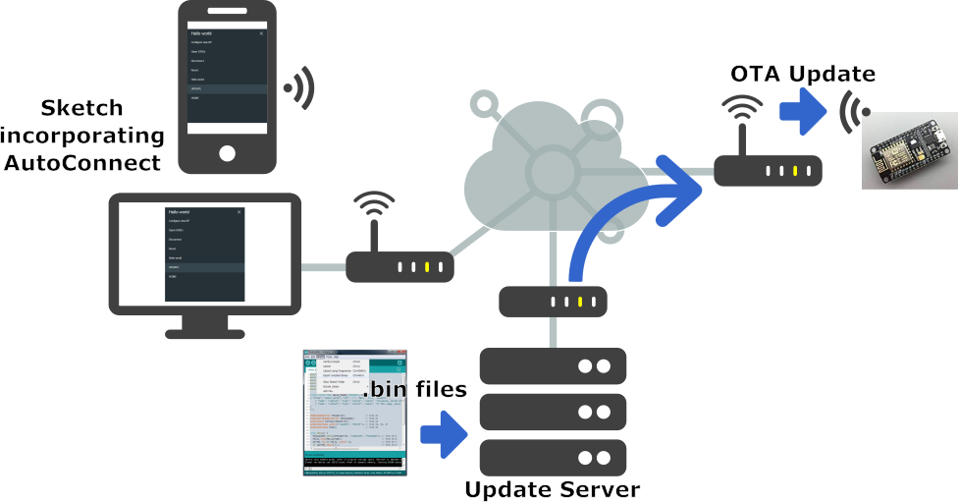
AutoConnect/docs/images/updatemodel.png
