Holtshad20/OMC_WIFI/AutoConnect/docs/images/updateserver.png

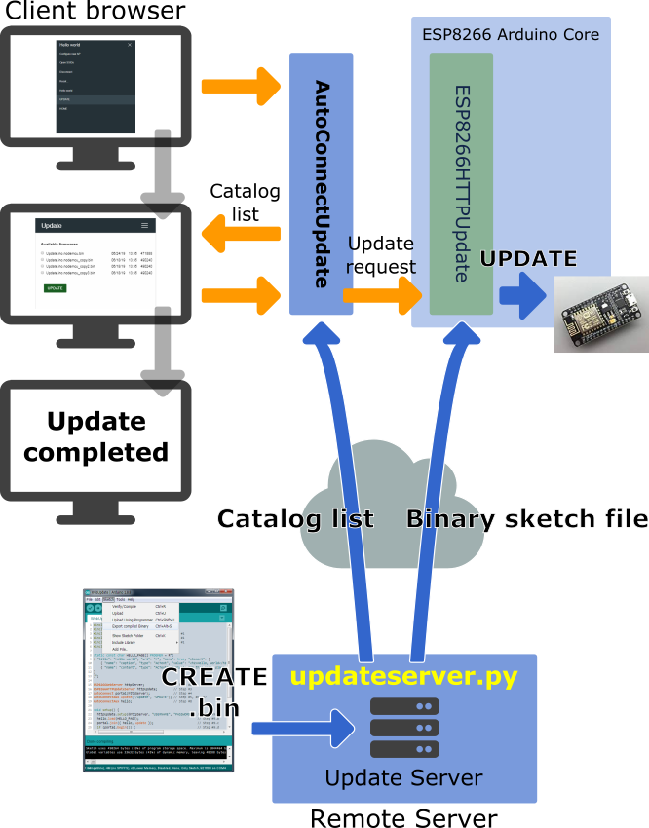
AutoConnect/docs/images/updateserver.png
