Holtshad20/OMC_WIFI/AutoConnect/docs/images/updating.png

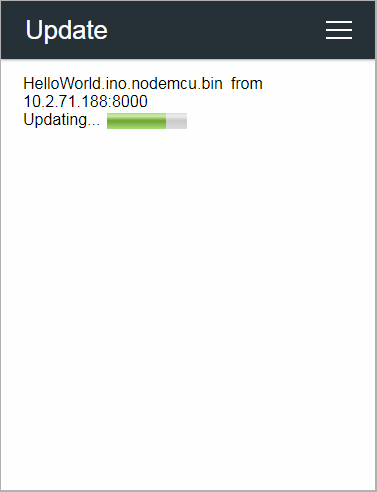
AutoConnect/docs/images/updating.png
