Holtshad20/OMC_WIFI/AutoConnect/docs/images/upload.gif

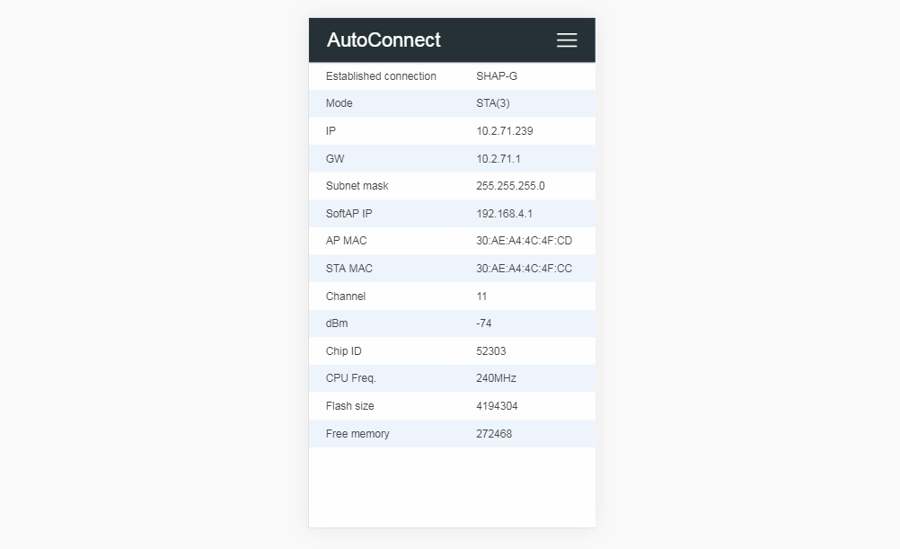
AutoConnect/docs/images/upload.gif
