Holtshad20/OMC_WIFI/AutoConnect/docs/images/USERKey.png

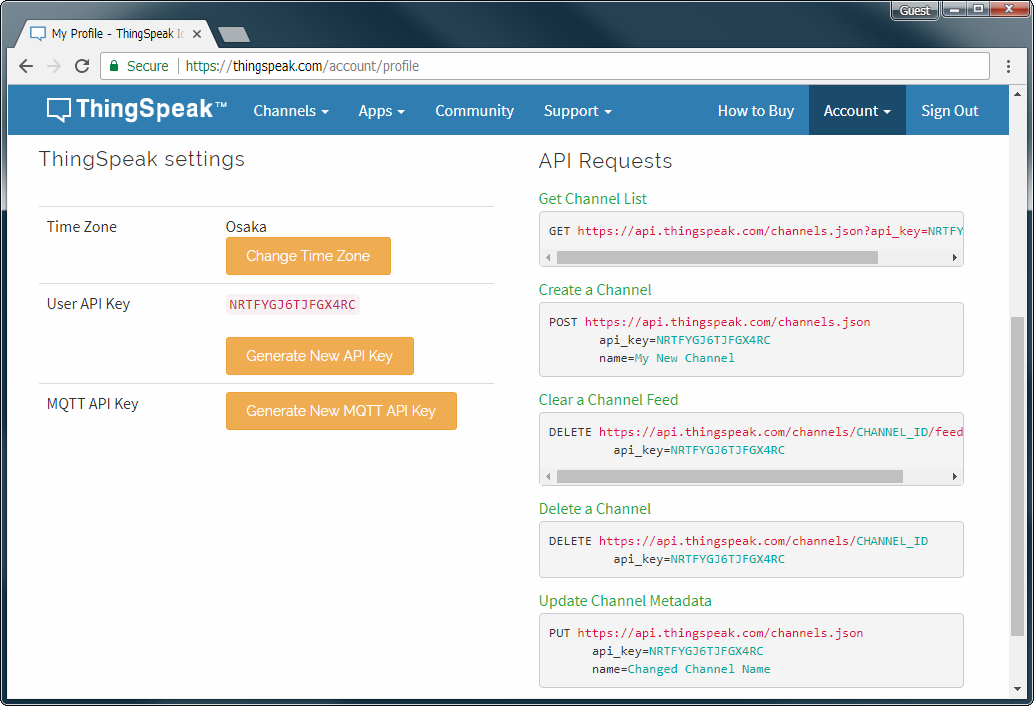
AutoConnect/docs/images/USERKey.png
