Holtshad20/OMC_WIFI/AutoConnect/docs/images/webcamserver_ss1.png

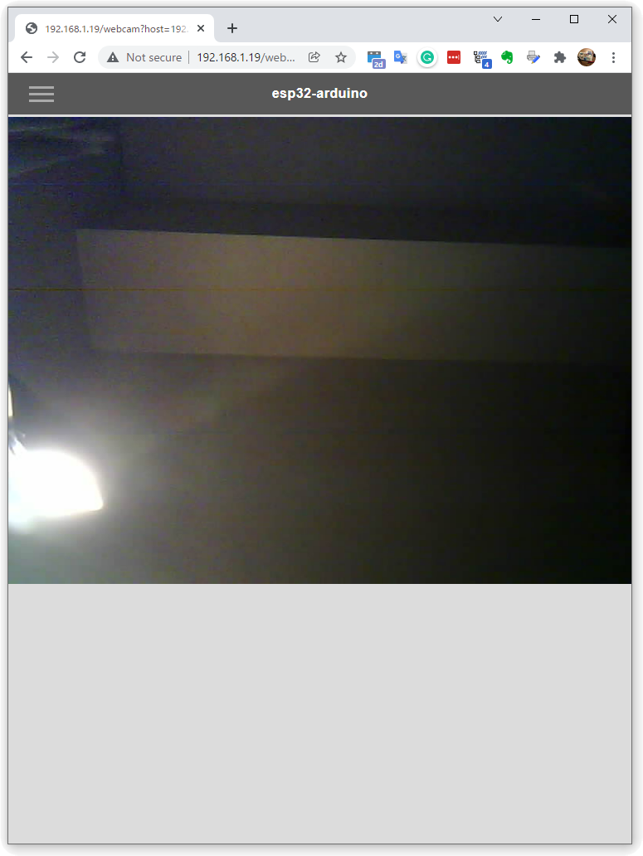
AutoConnect/docs/images/webcamserver_ss1.png
