Holtshad20/OMC_WIFI/AutoConnect/docs/images/webcamserver_ss2.png

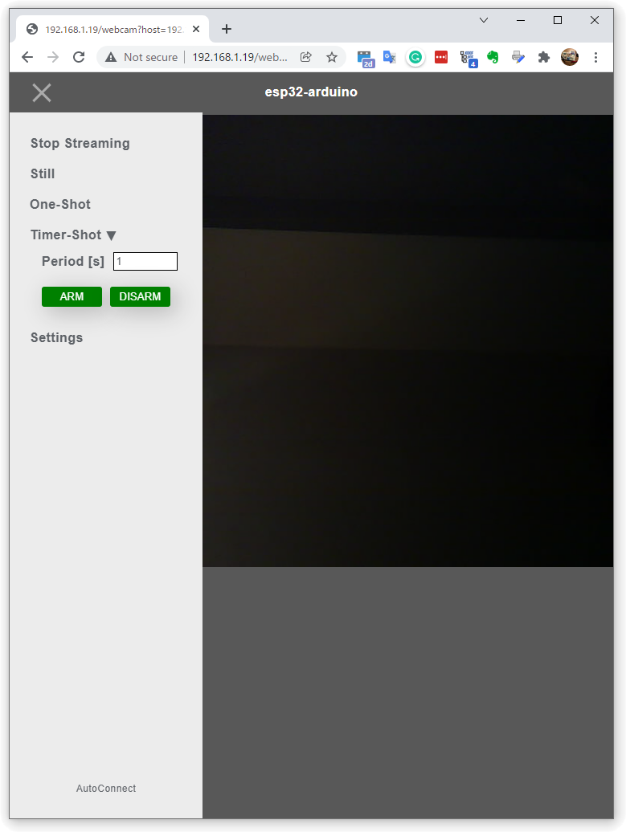
AutoConnect/docs/images/webcamserver_ss2.png
