Holtshad20/OMC_WIFI/AutoConnect/docs/images/webcamserver_ss3.png

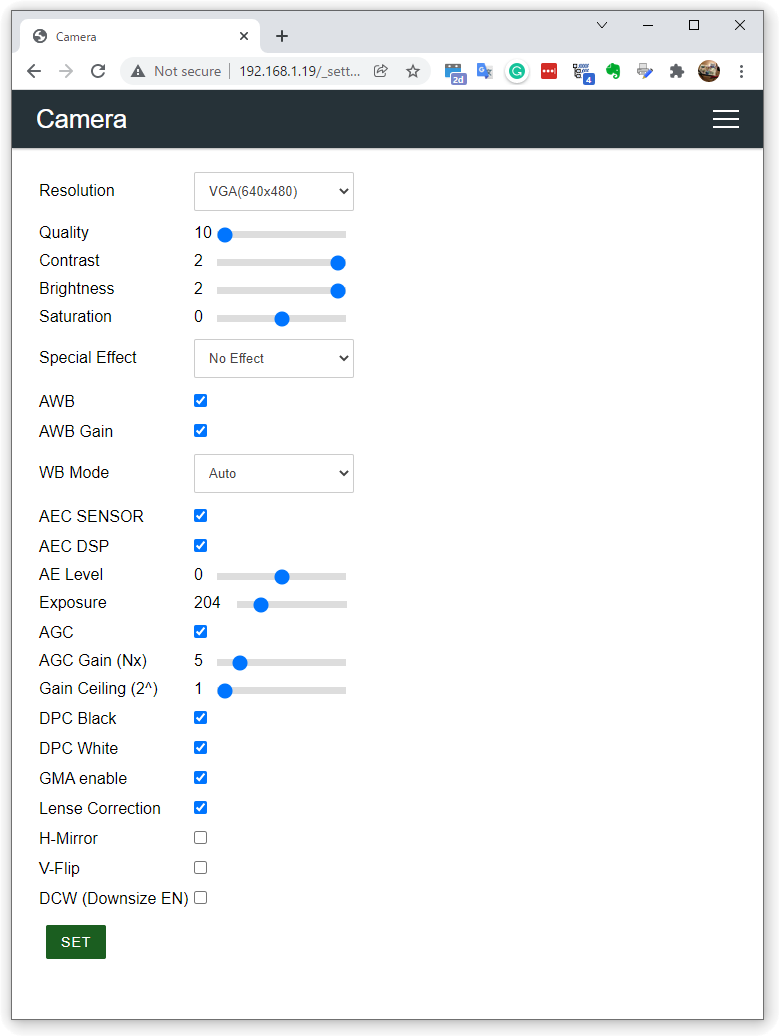
AutoConnect/docs/images/webcamserver_ss3.png
