Holtshad20/OMC_WIFI/AutoConnect/docs/images/webcamview_open.png

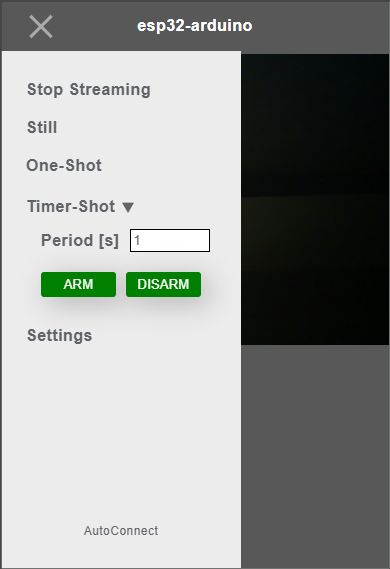
AutoConnect/docs/images/webcamview_open.png
