Holtshad20/OMC_WIFI/AutoConnect/docs/images/webcamview_set.png

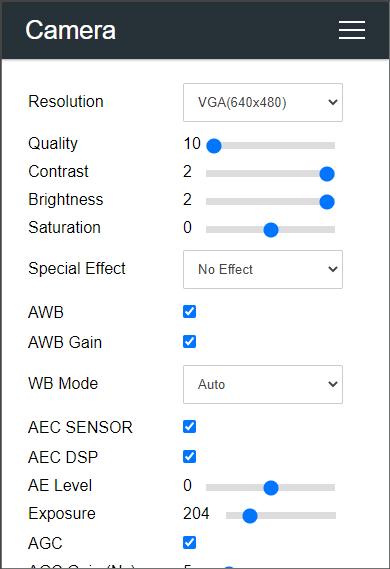
AutoConnect/docs/images/webcamview_set.png
