Holtshad20/OMC_WIFI/AutoConnect/docs/images/webupdate.gif

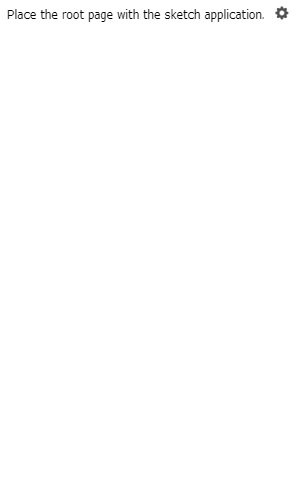
AutoConnect/docs/images/webupdate.gif
