Holtshad20/OMC_WIFI/AutoConnect/docs/images/webupdate.png

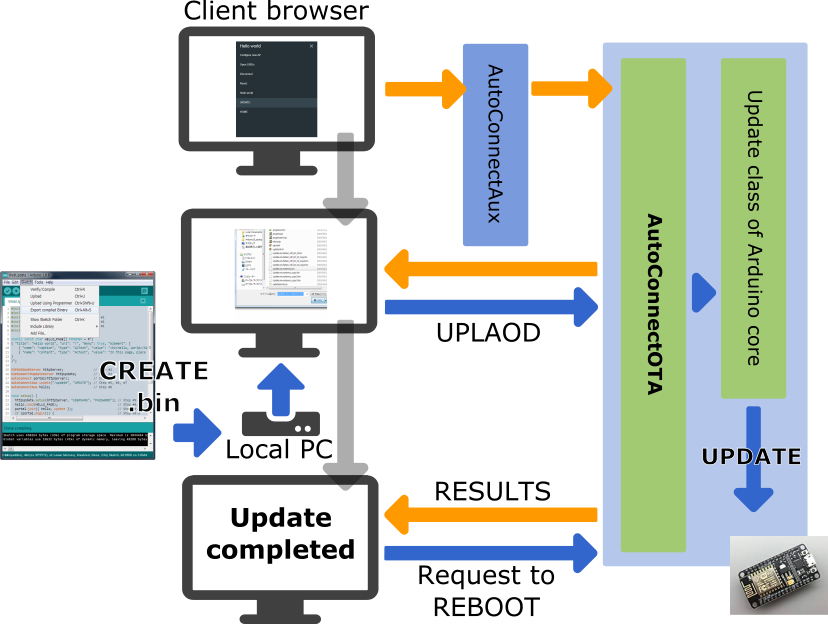
AutoConnect/docs/images/webupdate.png
