Holtshad20/OMC_WIFI/AutoConnect/docs/images/webupdatemodel.png

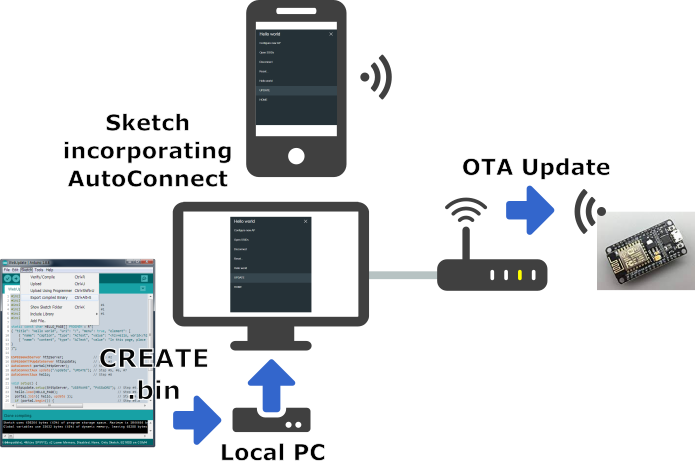
AutoConnect/docs/images/webupdatemodel.png
