Holtshad20/OMC_WIFI/AutoConnect/examples/FSBrowser/data/pins.png

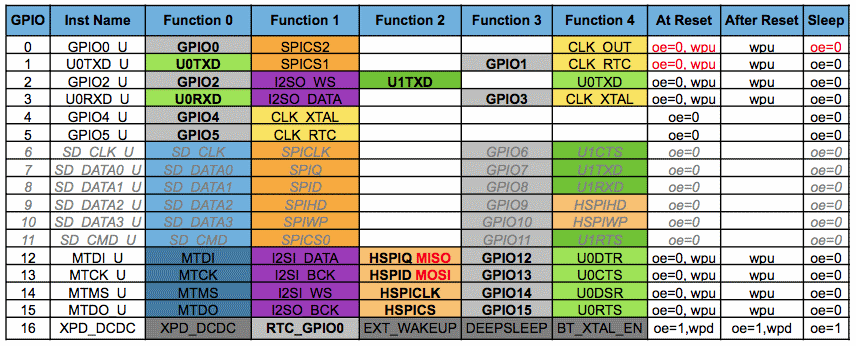
AutoConnect/examples/FSBrowser/data/pins.png
