Holtshad20/OMC_WIFI/OMC_PCB/PCBs v_1_0_1/OMC_SLAVE_v_1_0_1/SLAVE/Extras/SLAVE.png

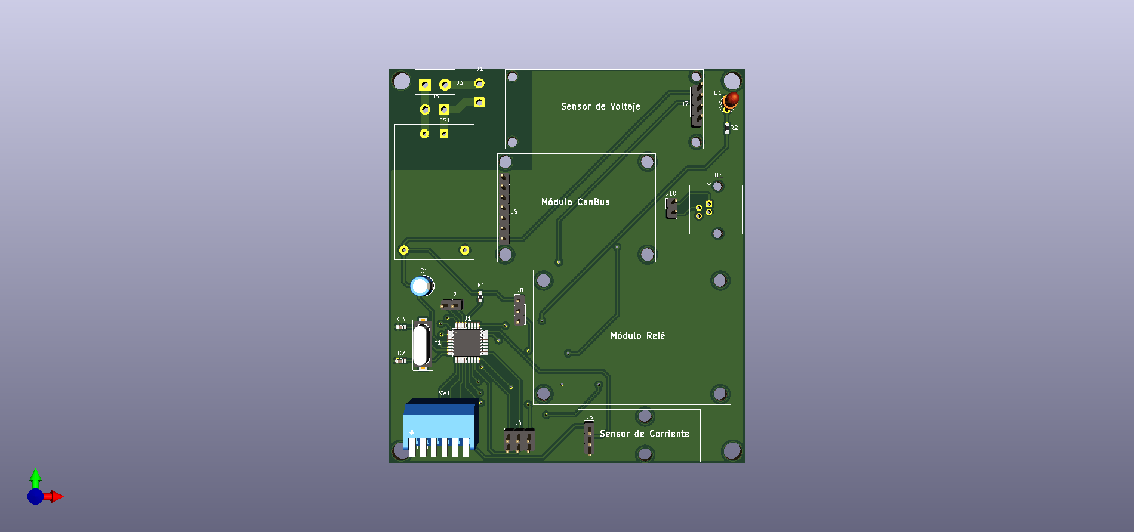
OMC_PCB/PCBs v_1_0_1/OMC_SLAVE_v_1_0_1/SLAVE/Extras/SLAVE.png
