Holtshad20/OMC_WIFI/AutoConnect/docs/images/PageBuilder.png

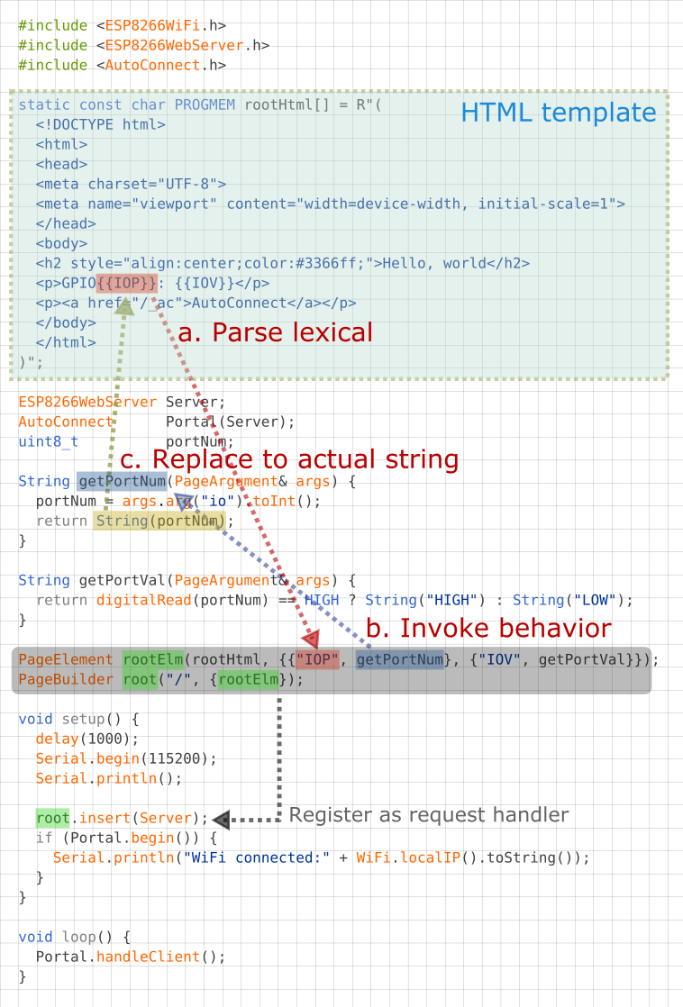
AutoConnect/docs/images/PageBuilder.png
