Holtshad20/OMC_WIFI/OMC_PCB/PCBs v_1_0_1/OMC_SLAVE_v_1_0_1/SLAVE/PDF/SLAVE-F_Mask.pdf

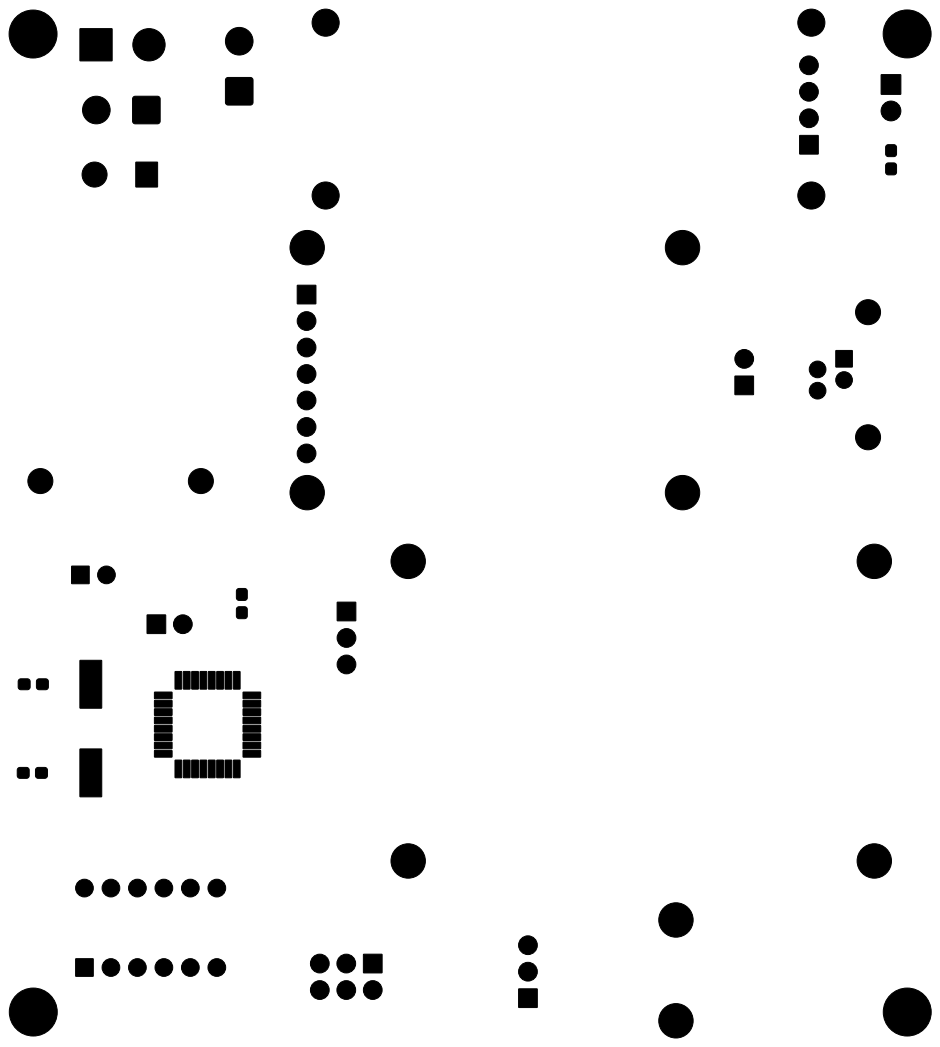
[picture p98: page 1]
