Holtshad20/OMC_WIFI/OMC_WIFI_PCB/V1.0/outputv2.pdf

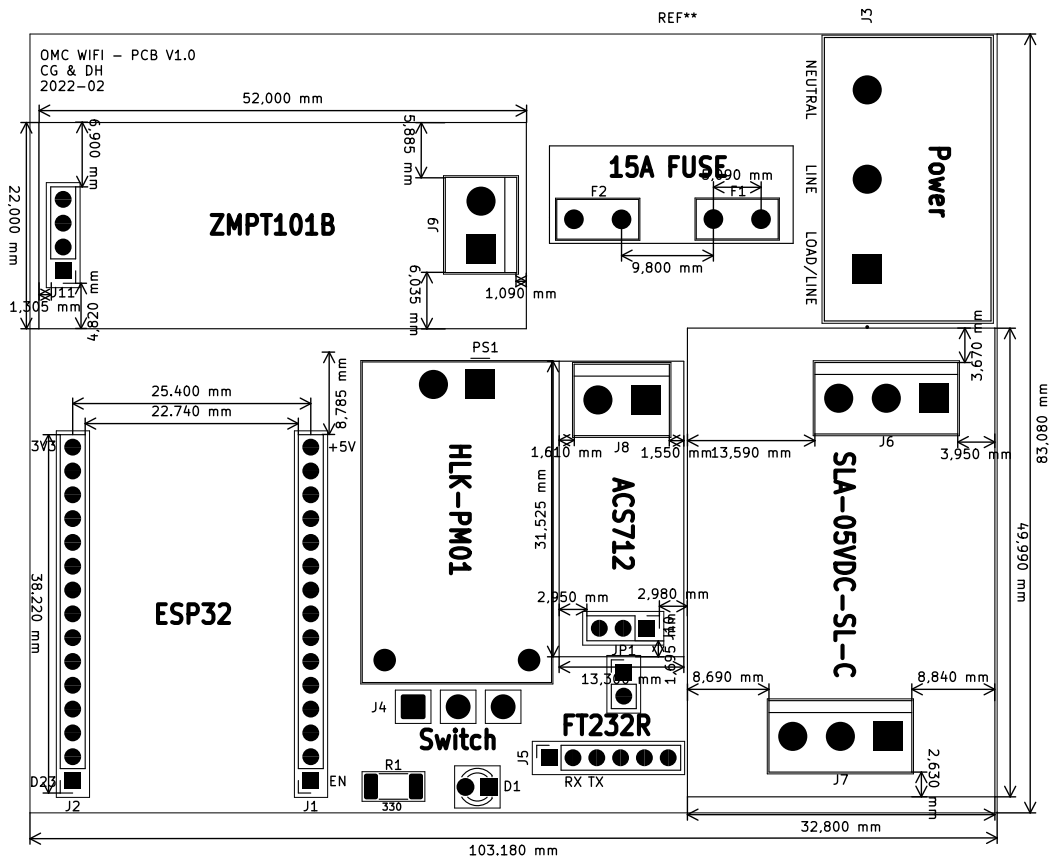
[picture p100: page 1]
